AndrewDykstra/Face-Tracking-Camera/opencv/sources/doc/tutorials/imgproc/histograms/back_projection/images/Back_Projection_Theory3.jpg

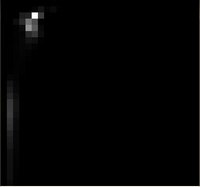
opencv/sources/doc/tutorials/imgproc/histograms/back_projection/images/Back_Projection_Theory3.jpg
