AndrewDykstra/Face-Tracking-Camera/opencv/sources/doc/tutorials/imgproc/histograms/back_projection/images/Back_Projection_Theory4.jpg

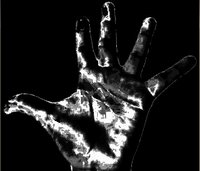
opencv/sources/doc/tutorials/imgproc/histograms/back_projection/images/Back_Projection_Theory4.jpg
