AndrewDykstra/Face-Tracking-Camera/opencv/sources/doc/tutorials/imgproc/histograms/histogram_calculation/images/Histogram_Calculation_Theory_Hist1.jpg

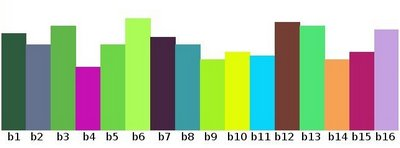
opencv/sources/doc/tutorials/imgproc/histograms/histogram_calculation/images/Histogram_Calculation_Theory_Hist1.jpg
