AndrewDykstra/Face-Tracking-Camera/opencv/sources/doc/tutorials/imgproc/histograms/histogram_equalization/images/Histogram_Equalization_Theory_1.jpg

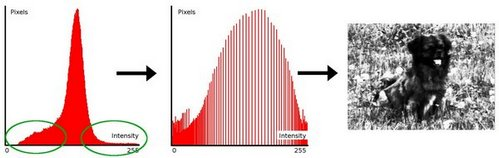
opencv/sources/doc/tutorials/imgproc/histograms/histogram_equalization/images/Histogram_Equalization_Theory_1.jpg
