AndrewDykstra/Face-Tracking-Camera/opencv/sources/doc/tutorials/imgproc/histograms/template_matching/images/Template_Matching_Template_Theory_Summary.jpg

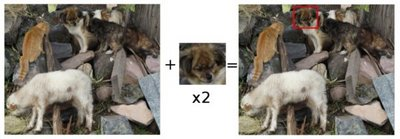
opencv/sources/doc/tutorials/imgproc/histograms/template_matching/images/Template_Matching_Template_Theory_Summary.jpg
