AndrewDykstra/Face-Tracking-Camera/3D Model Parts and Assembly/ArduinoUno/blm21.SLDPRT

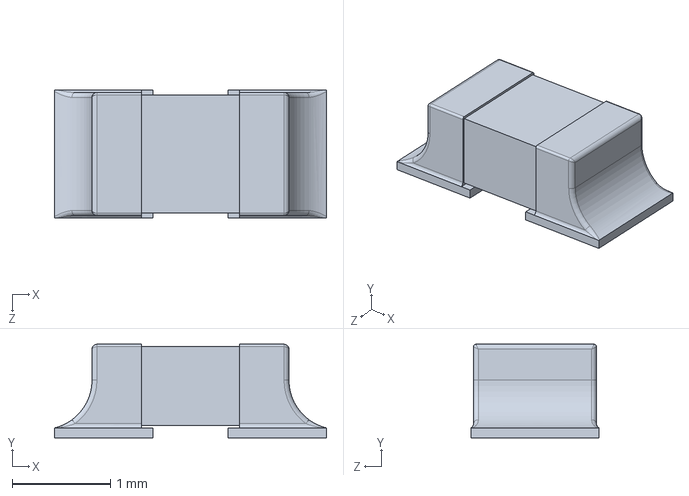
[picture p27: CAD file, 2022-12-01]
3D Model Parts and Assembly/ArduinoUno/blm21.SLDPRT
2.76 x 0.95 x 1.30 mm
