AndrewDykstra/Face-Tracking-Camera/3D Model Parts and Assembly/ArduinoUno/atmega16u2.SLDPRT

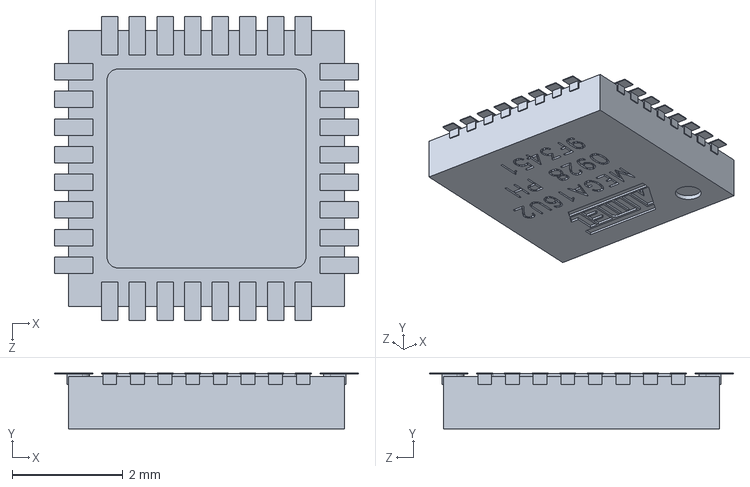
[picture p28: CAD file, 2022-12-01]
3D Model Parts and Assembly/ArduinoUno/atmega16u2.SLDPRT
5.50 x 1.01 x 5.50 mm
