AndrewDykstra/Face-Tracking-Camera/3D Model Parts and Assembly/ArduinoUno/6 PORT HEADER.SLDPRT

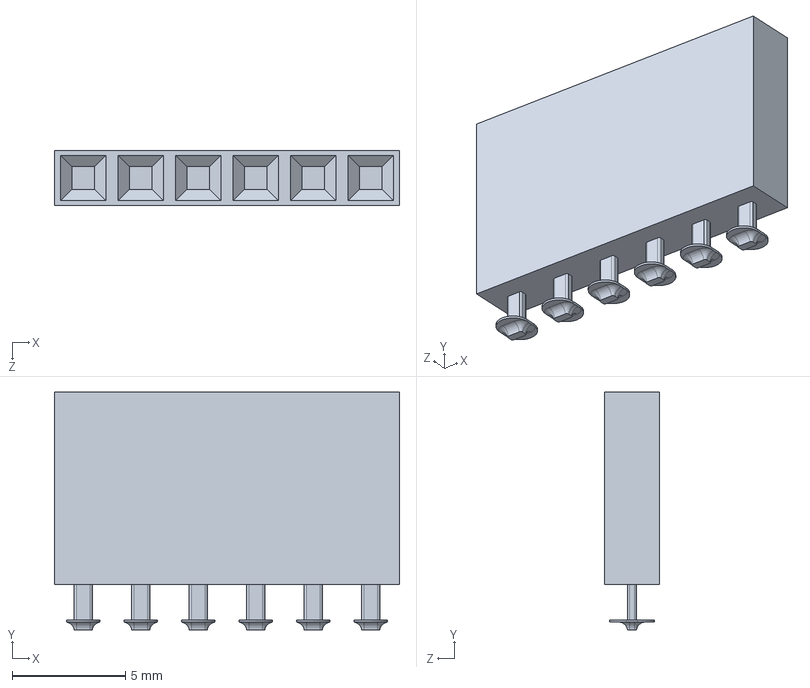
[picture p29: CAD file, 2022-12-01]
3D Model Parts and Assembly/ArduinoUno/6 PORT HEADER.SLDPRT
15.2 x 10.5 x 2.41 mm
