AndrewDykstra/Face-Tracking-Camera/3D Model Parts and Assembly/Logitech_C920.SLDPRT

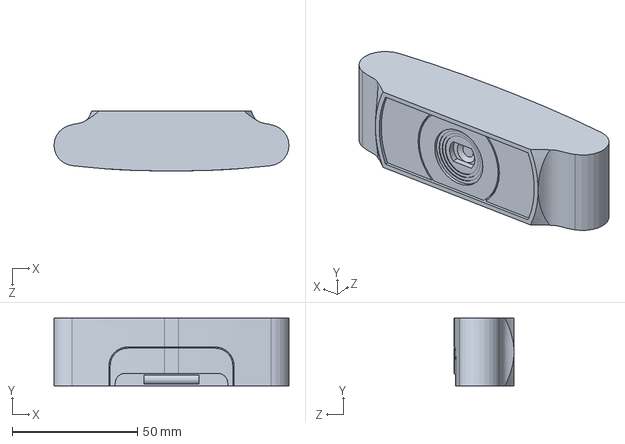
[picture p30: CAD file, 2022-12-01]
3D Model Parts and Assembly/Logitech_C920.SLDPRT
94.0 x 27.0 x 24.0 mm
