AndrewDykstra/Face-Tracking-Camera/3D Model Parts and Assembly/ArduinoUno/603 cap on pad.SLDPRT

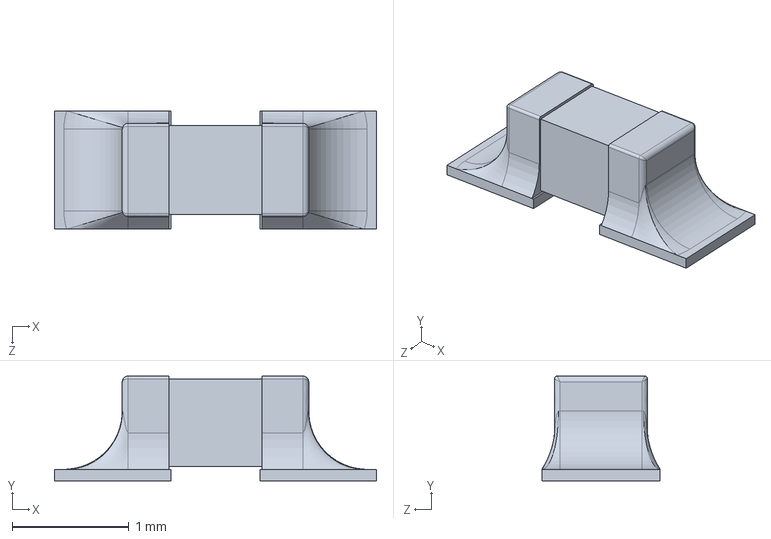
[picture p31: CAD file, 2022-12-01]
3D Model Parts and Assembly/ArduinoUno/603 cap on pad.SLDPRT
2.76 x 0.9 x 1.02 mm
