AndrewDykstra/Face-Tracking-Camera/3D Model Parts and Assembly/pantilt.STEP

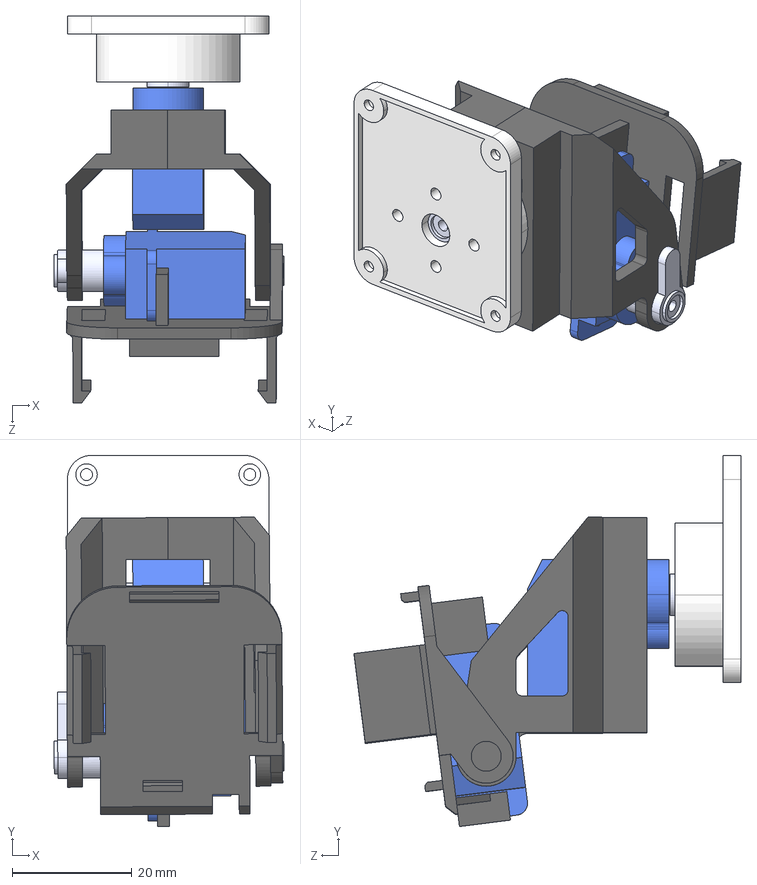
[picture p32: CAD file, 2022-12-01]
3D Model Parts and Assembly/pantilt.STEP
38.4 x 62.1 x 64.7 mm
pantilt_1_Domyslna
servo_emax_9g_horn_Domyslna
servo_emax_9g_main_body_Domyslna x 2
pantilt_2_left_Domyslna
pantilt_2_right_Domyslna
servo_emax_9g_horn_2_Domyslna
pantilt_3_Domyslna
