AndrewDykstra/Face-Tracking-Camera/3D Model Parts and Assembly/ArduinoUno/cd1206 diode.SLDPRT

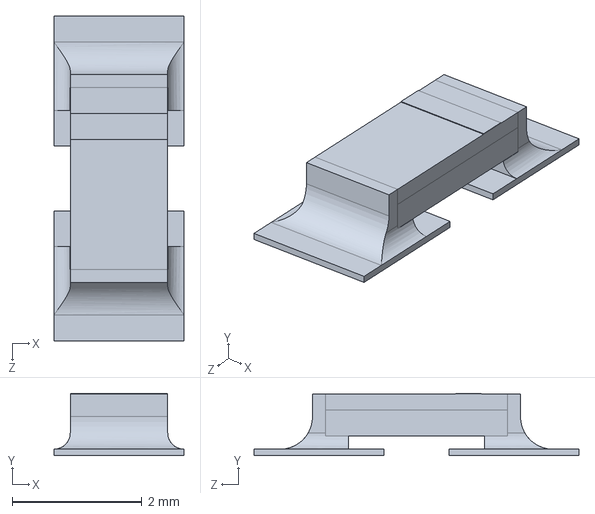
[picture p33: CAD file, 2022-12-01]
3D Model Parts and Assembly/ArduinoUno/cd1206 diode.SLDPRT
2.00 x 0.96 x 5.00 mm
