AndrewDykstra/Face-Tracking-Camera/3D Model Parts and Assembly/IphoneBox.SLDPRT

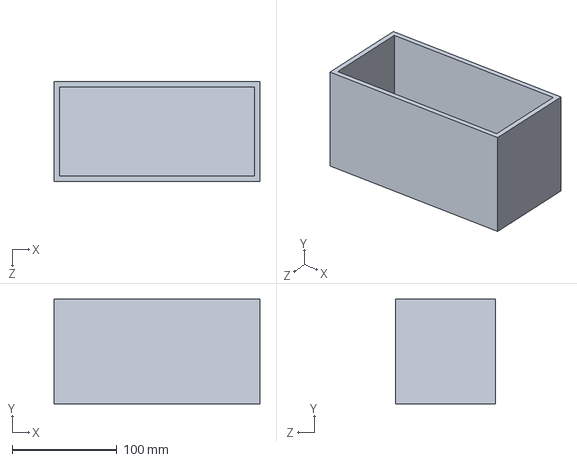
[picture p34: CAD file, 2022-12-01]
3D Model Parts and Assembly/IphoneBox.SLDPRT
196.9 x 100.3 x 95.2 mm
