AndrewDykstra/Face-Tracking-Camera/3D Model Parts and Assembly/ArduinoUno/16mhz crystal - measured.SLDPRT

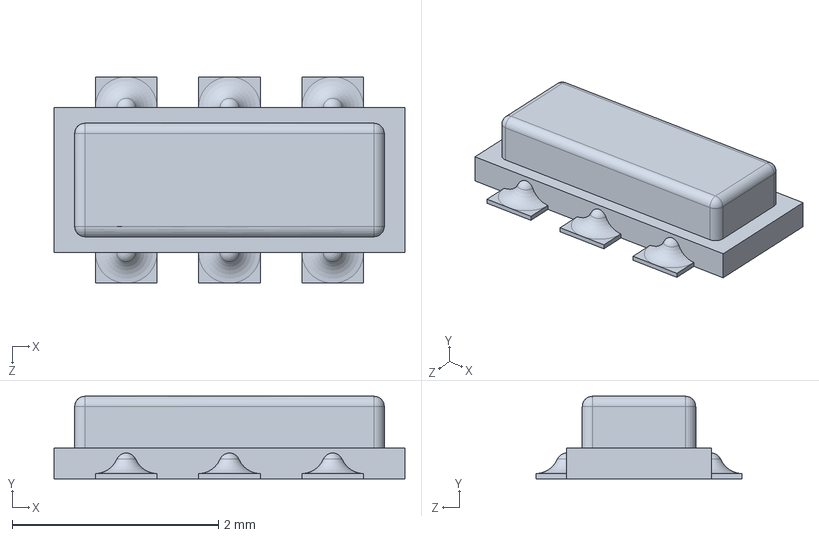
[picture p35: CAD file, 2022-12-01]
3D Model Parts and Assembly/ArduinoUno/16mhz crystal - measured.SLDPRT
3.40 x 0.8 x 2.00 mm
