AndrewDykstra/Face-Tracking-Camera/3D Model Parts and Assembly/pantilt_1.SLDPRT

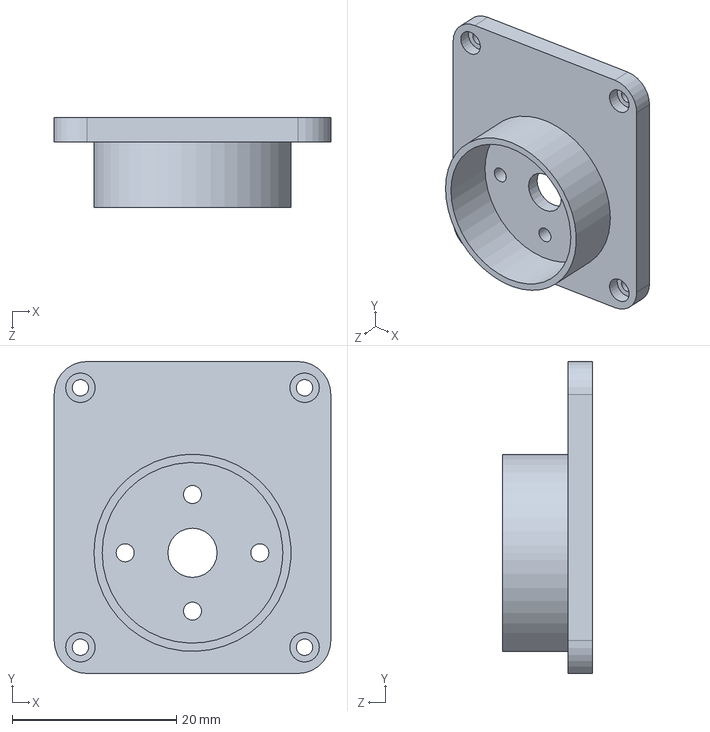
[picture p36: CAD file, 2022-12-01]
3D Model Parts and Assembly/pantilt_1.SLDPRT
33.7 x 38.0 x 11.0 mm
