AndrewDykstra/Face-Tracking-Camera/3D Model Parts and Assembly/ArduinoUno/PADS001.SLDPRT

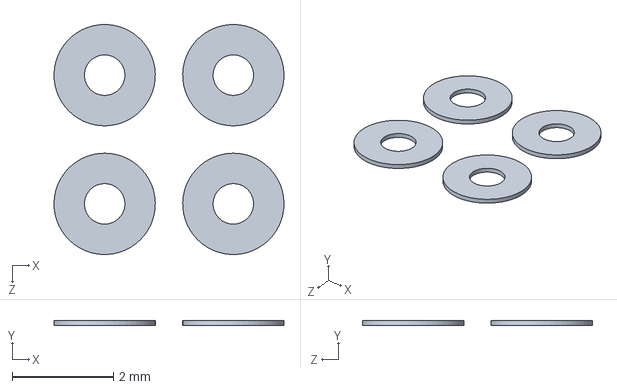
[picture p37: CAD file, 2022-12-01]
3D Model Parts and Assembly/ArduinoUno/PADS001.SLDPRT
4.54 x 0.1 x 4.54 mm
