AndrewDykstra/Face-Tracking-Camera/3D Model Parts and Assembly/pantilt_3.SLDPRT

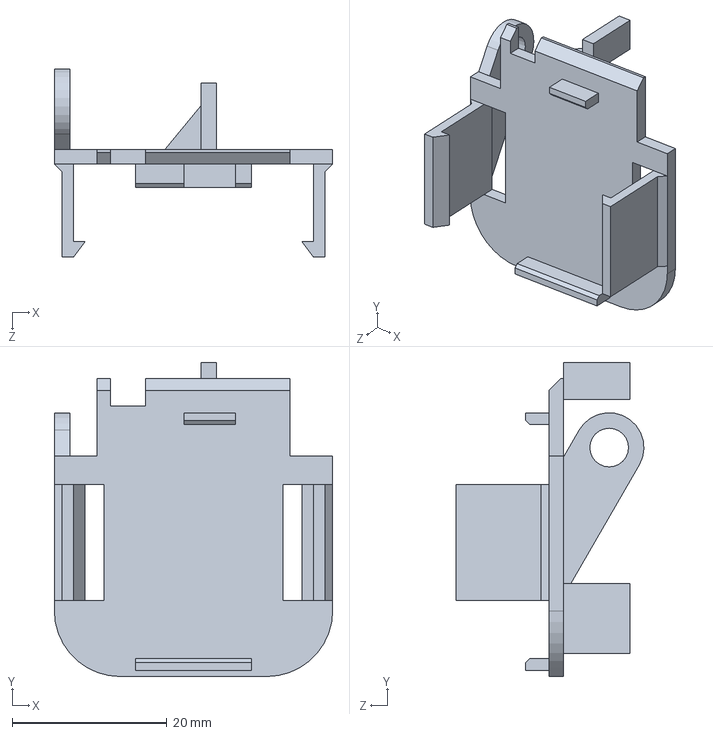
[picture p38: CAD file, 2022-12-01]
3D Model Parts and Assembly/pantilt_3.SLDPRT
36.0 x 40.6 x 24.3 mm
