AndrewDykstra/Face-Tracking-Camera/3D Model Parts and Assembly/pantilt_2_left.SLDPRT

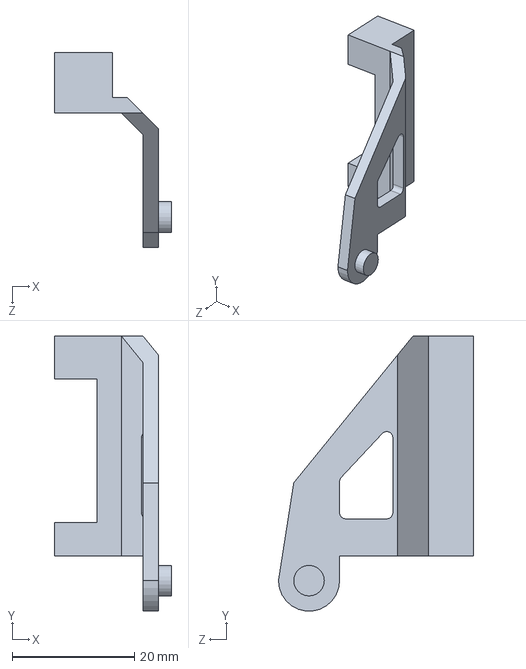
[picture p39: CAD file, 2022-12-01]
3D Model Parts and Assembly/pantilt_2_left.SLDPRT
19.2 x 45.0 x 31.9 mm
