AndrewDykstra/Face-Tracking-Camera/3D Model Parts and Assembly/ArduinoUno/led.SLDPRT

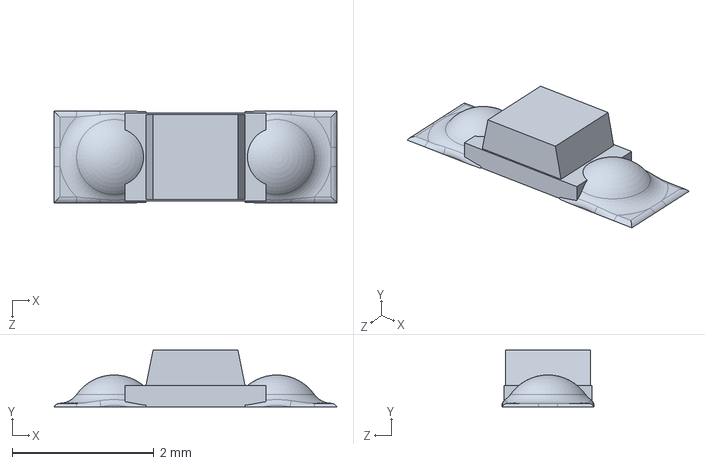
[picture p40: CAD file, 2022-12-01]
3D Model Parts and Assembly/ArduinoUno/led.SLDPRT
4.00 x 0.8 x 1.30 mm
