AndrewDykstra/Face-Tracking-Camera/3D Model Parts and Assembly/Logitech_C920Glass.SLDPRT

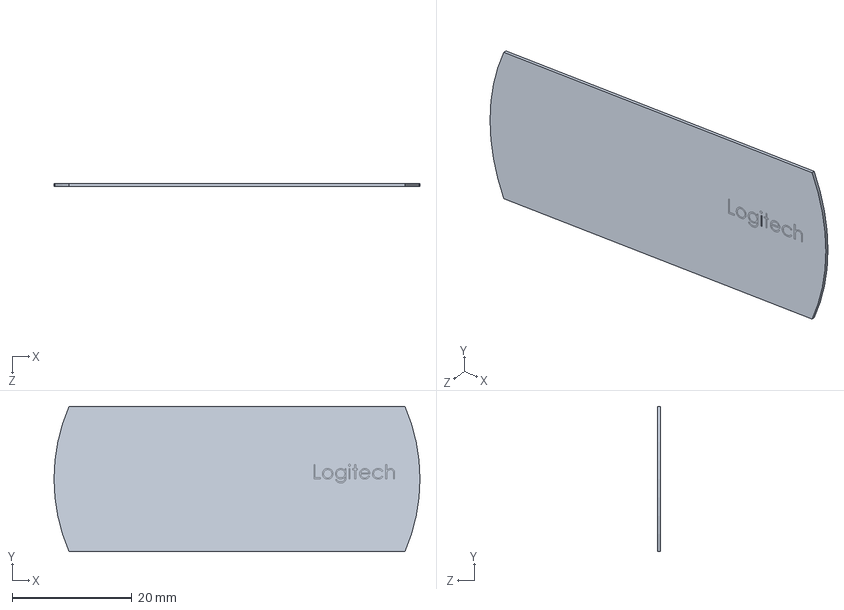
[picture p41: CAD file, 2022-12-01]
3D Model Parts and Assembly/Logitech_C920Glass.SLDPRT
61.0 x 24.2 x 0.51 mm
