AndrewDykstra/Face-Tracking-Camera/3D Model Parts and Assembly/ArduinoUno/10 PORT HEADER.SLDPRT

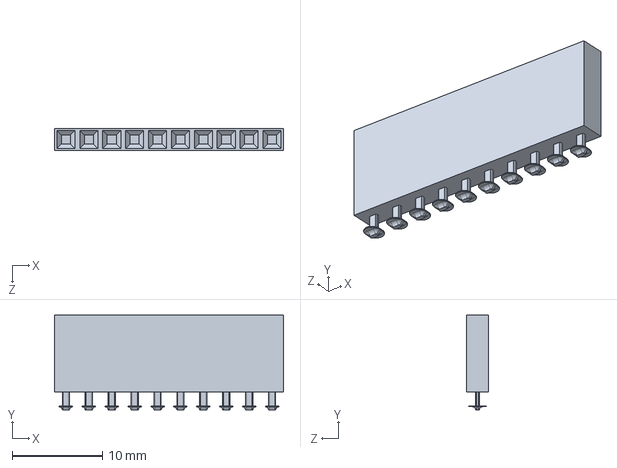
[picture p42: CAD file, 2022-12-01]
3D Model Parts and Assembly/ArduinoUno/10 PORT HEADER.SLDPRT
25.4 x 10.5 x 2.41 mm
