AndrewDykstra/Face-Tracking-Camera/3D Model Parts and Assembly/servo_emax_9g_horn_2.SLDPRT

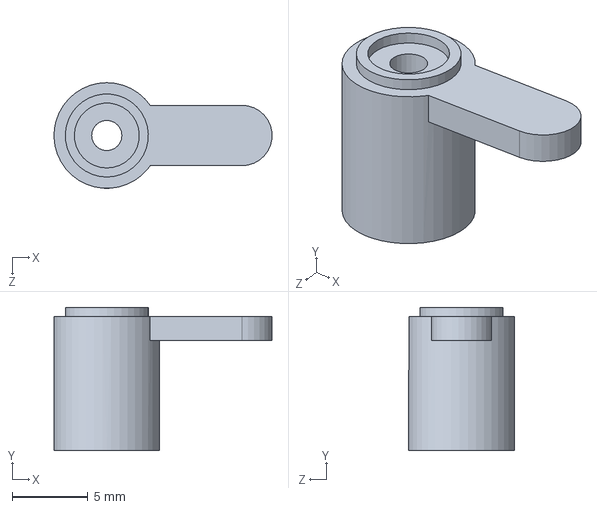
[picture p43: CAD file, 2022-12-01]
3D Model Parts and Assembly/servo_emax_9g_horn_2.SLDPRT
14.4 x 9.50 x 7.00 mm
