AndrewDykstra/Face-Tracking-Camera/3D Model Parts and Assembly/ArduinoUno/crystal.sldprt

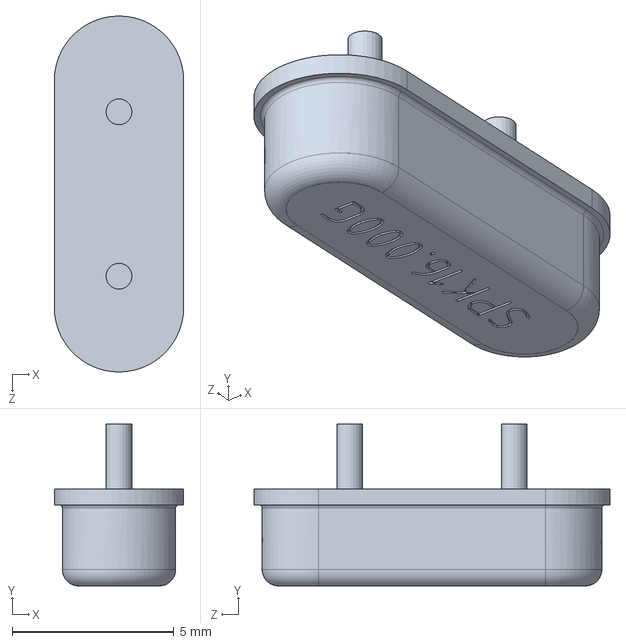
[picture p44: CAD file, 2022-12-01]
3D Model Parts and Assembly/ArduinoUno/crystal.sldprt
4.00 x 5.00 x 11.0 mm
