AndrewDykstra/Face-Tracking-Camera/3D Model Parts and Assembly/servo_emax_9g_horn.SLDPRT

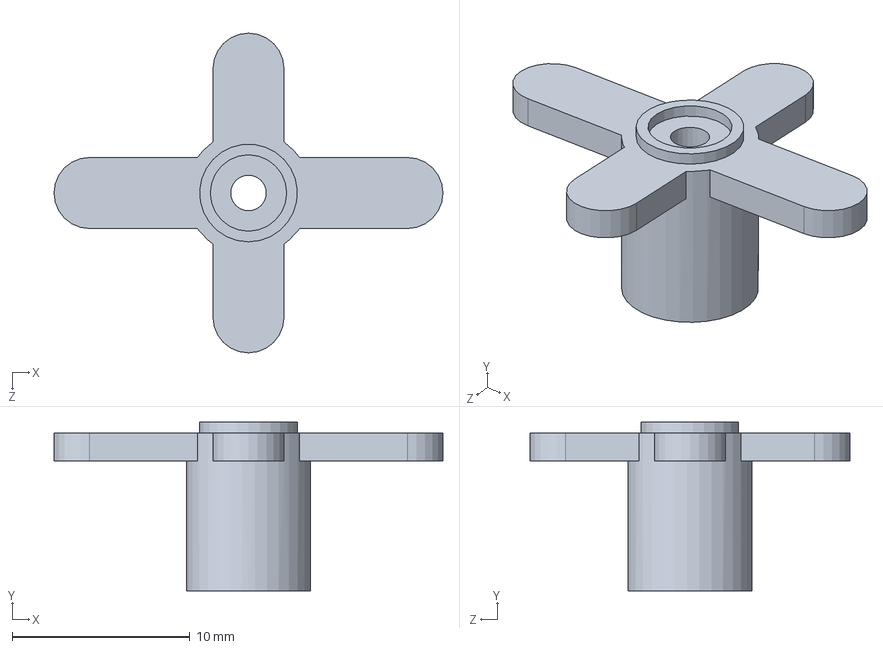
[picture p45: CAD file, 2022-12-01]
3D Model Parts and Assembly/servo_emax_9g_horn.SLDPRT
21.9 x 9.50 x 18.0 mm
