AndrewDykstra/Face-Tracking-Camera/3D Model Parts and Assembly/ArduinoUno/dip socket pin.SLDPRT

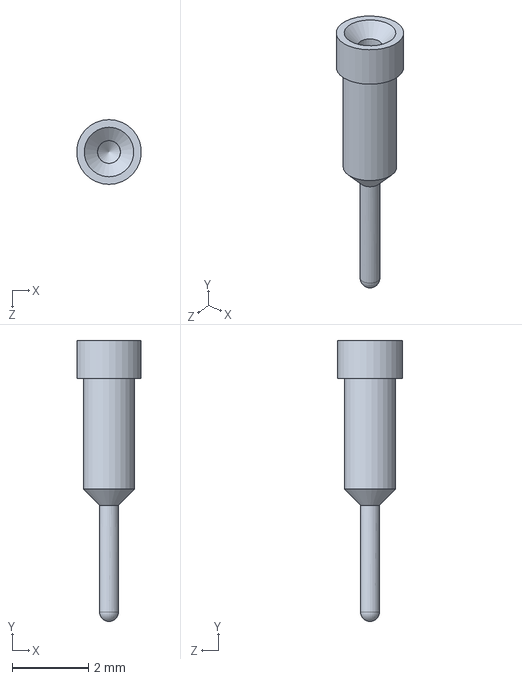
[picture p46: CAD file, 2022-12-01]
3D Model Parts and Assembly/ArduinoUno/dip socket pin.SLDPRT
1.69 x 7.37 x 1.70 mm
