AndrewDykstra/Face-Tracking-Camera/3D Model Parts and Assembly/matrix.SLDPRT

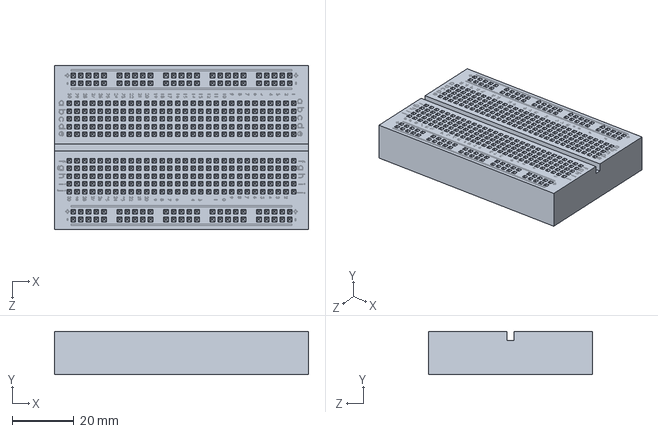
[picture p47: CAD file, 2022-12-01]
3D Model Parts and Assembly/matrix.SLDPRT
82.0 x 14.0 x 53.0 mm
