AndrewDykstra/Face-Tracking-Camera/3D Model Parts and Assembly/ArduinoUno/103 RESISTOR PACK.SLDPRT

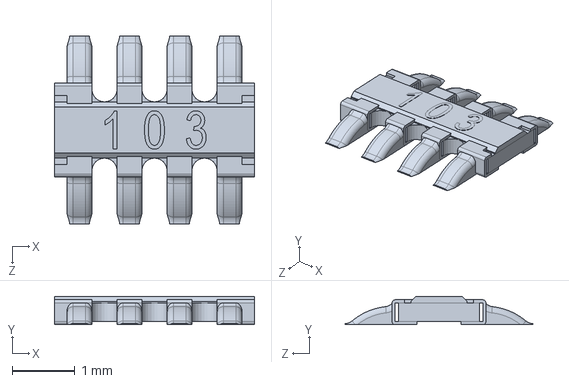
[picture p48: CAD file, 2022-12-01]
3D Model Parts and Assembly/ArduinoUno/103 RESISTOR PACK.SLDPRT
3.20 x 0.455 x 3.00 mm
