AndrewDykstra/Face-Tracking-Camera/3D Model Parts and Assembly/ArduinoUno/RESET CORE.SLDPRT

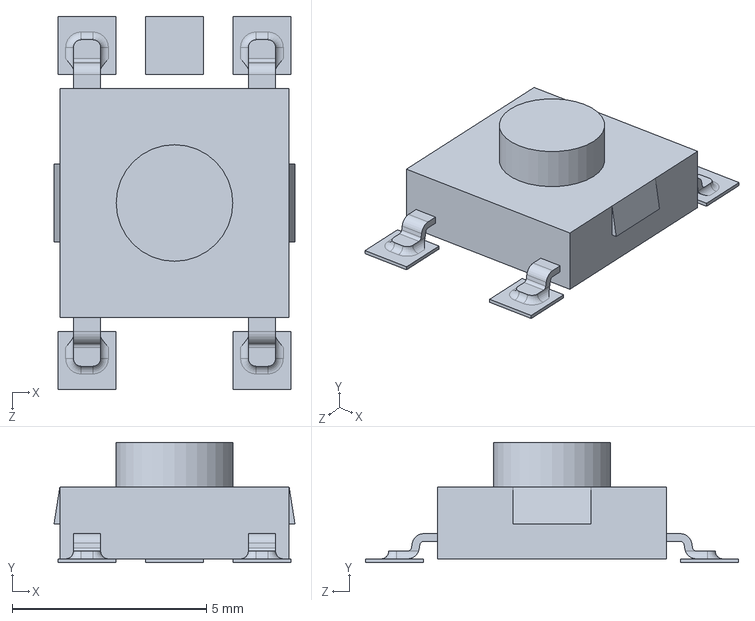
[picture p49: CAD file, 2022-12-01]
3D Model Parts and Assembly/ArduinoUno/RESET CORE.SLDPRT
6.20 x 3.10 x 9.60 mm
