AndrewDykstra/Face-Tracking-Camera/3D Model Parts and Assembly/ArduinoUno/usb top contact.SLDPRT

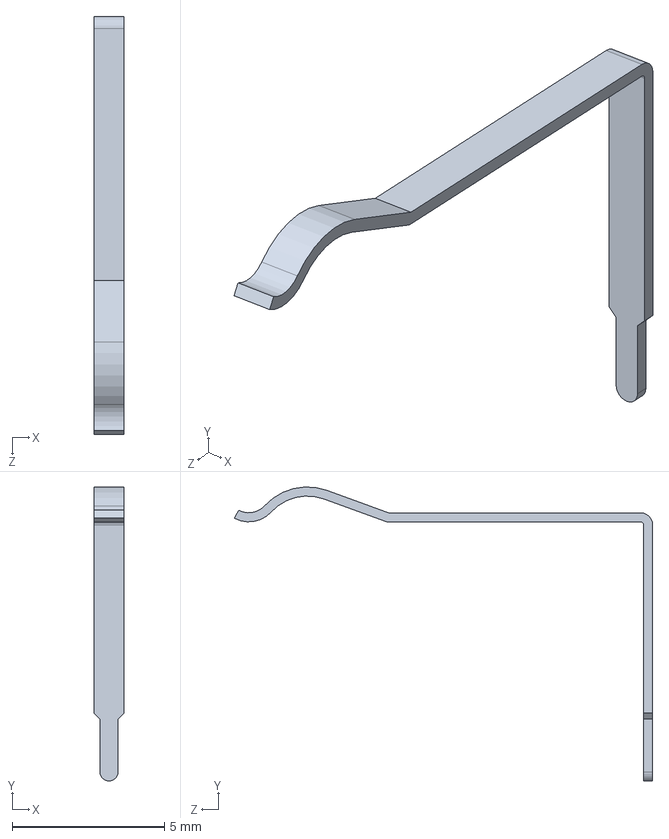
[picture p50: CAD file, 2022-12-01]
3D Model Parts and Assembly/ArduinoUno/usb top contact.SLDPRT
1.00 x 9.67 x 13.8 mm
