AndrewDykstra/Face-Tracking-Camera/3D Model Parts and Assembly/ArduinoUno/usb btm contact.SLDPRT

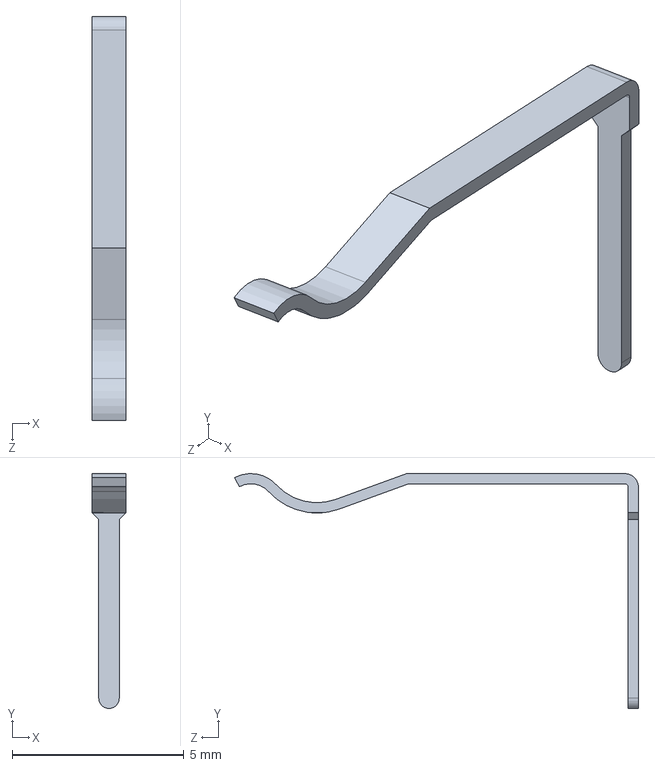
[picture p51: CAD file, 2022-12-01]
3D Model Parts and Assembly/ArduinoUno/usb btm contact.SLDPRT
1.00 x 6.84 x 11.8 mm
