AndrewDykstra/Face-Tracking-Camera/3D Model Parts and Assembly/ArduinoUno/lp2985dgkr.SLDPRT

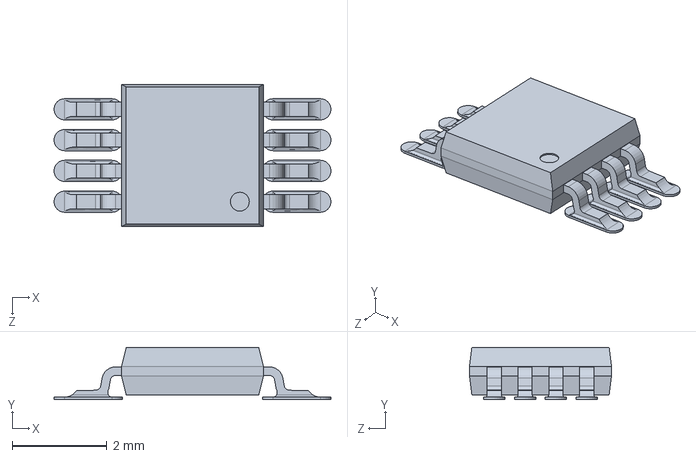
[picture p52: CAD file, 2022-12-01]
3D Model Parts and Assembly/ArduinoUno/lp2985dgkr.SLDPRT
5.85 x 1.10 x 3.00 mm
