AndrewDykstra/Face-Tracking-Camera/3D Model Parts and Assembly/ArduinoUno/mf-msmf050-2.SLDPRT

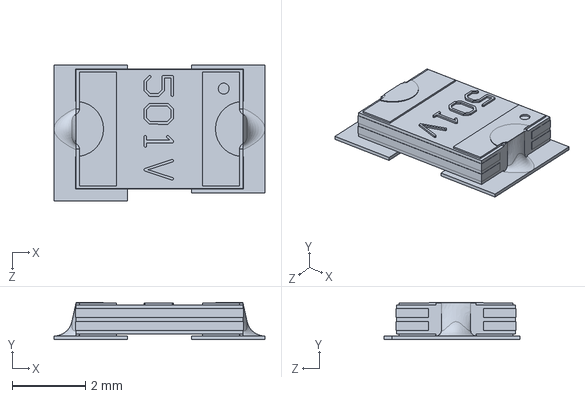
[picture p53: CAD file, 2022-12-01]
3D Model Parts and Assembly/ArduinoUno/mf-msmf050-2.SLDPRT
5.75 x 1.02 x 3.72 mm
