AndrewDykstra/Face-Tracking-Camera/3D Model Parts and Assembly/ArduinoUno/nano - reg.SLDPRT

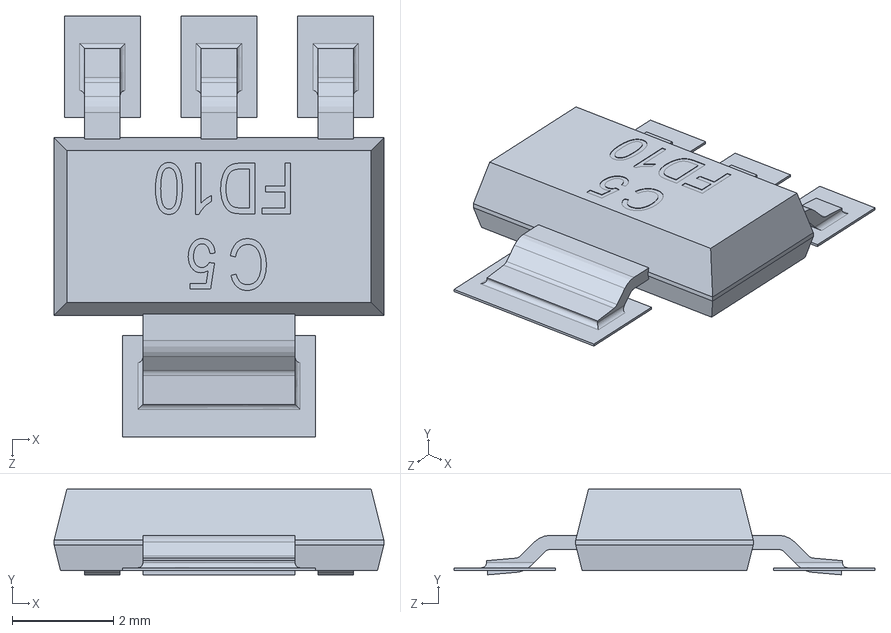
[picture p54: CAD file, 2022-12-01]
3D Model Parts and Assembly/ArduinoUno/nano - reg.SLDPRT
6.50 x 1.69 x 8.30 mm
