AndrewDykstra/Face-Tracking-Camera/3D Model Parts and Assembly/ArduinoUno/ATMEL328P.SLDPRT

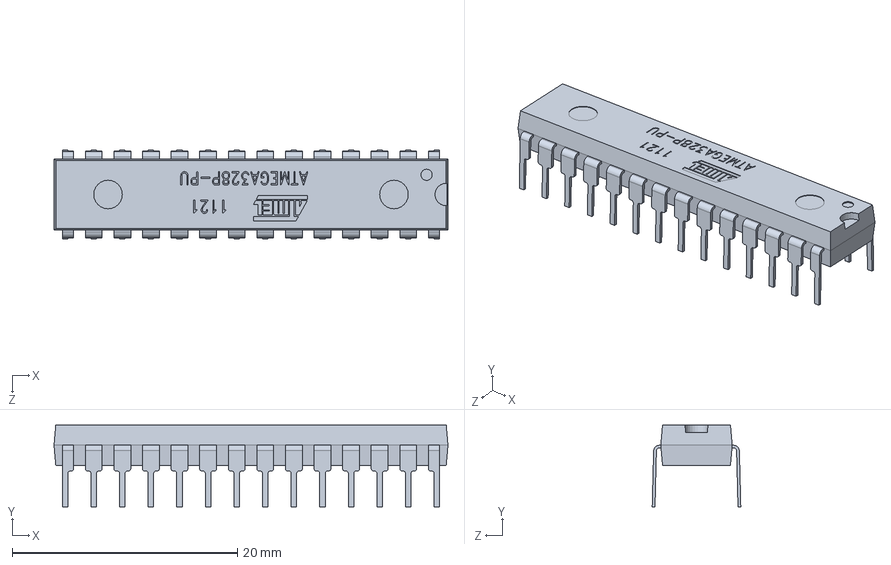
[picture p55: CAD file, 2022-12-01]
3D Model Parts and Assembly/ArduinoUno/ATMEL328P.SLDPRT
35.0 x 7.27 x 7.87 mm
