AndrewDykstra/Face-Tracking-Camera/3D Model Parts and Assembly/ArduinoUno/47uf CAP Dcase.SLDPRT

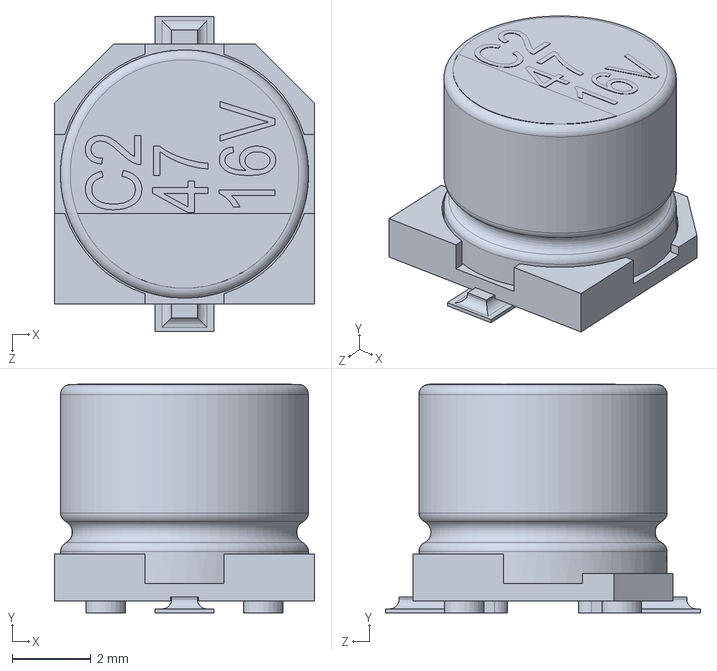
[picture p56: CAD file, 2022-12-01]
3D Model Parts and Assembly/ArduinoUno/47uf CAP Dcase.SLDPRT
6.60 x 5.81 x 8.00 mm
