AndrewDykstra/Face-Tracking-Camera/3D Model Parts and Assembly/ArduinoUno/m7 diode.SLDPRT

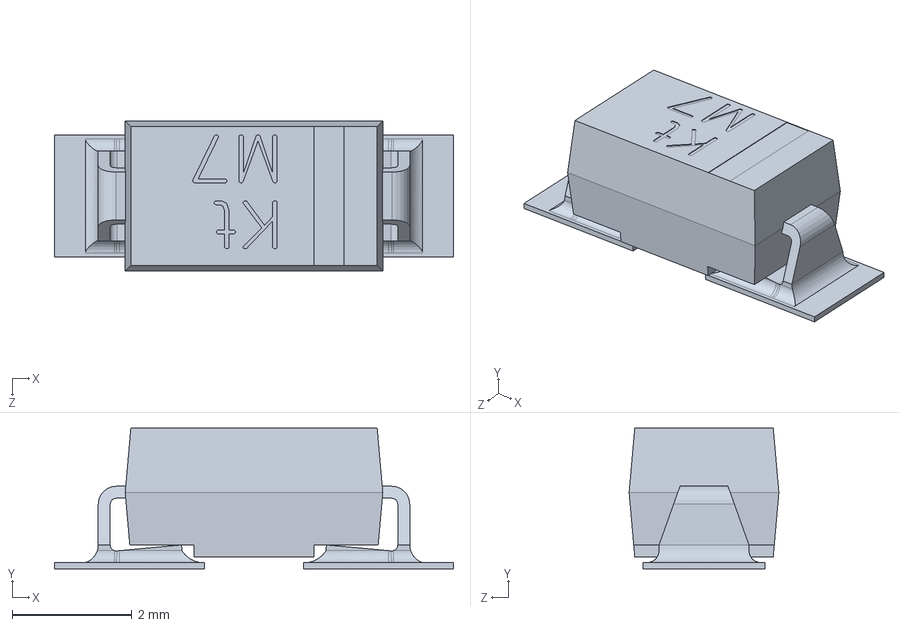
[picture p57: CAD file, 2022-12-01]
3D Model Parts and Assembly/ArduinoUno/m7 diode.SLDPRT
6.66 x 2.35 x 2.50 mm
