AndrewDykstra/Face-Tracking-Camera/3D Model Parts and Assembly/ArduinoUno/USB core.SLDPRT

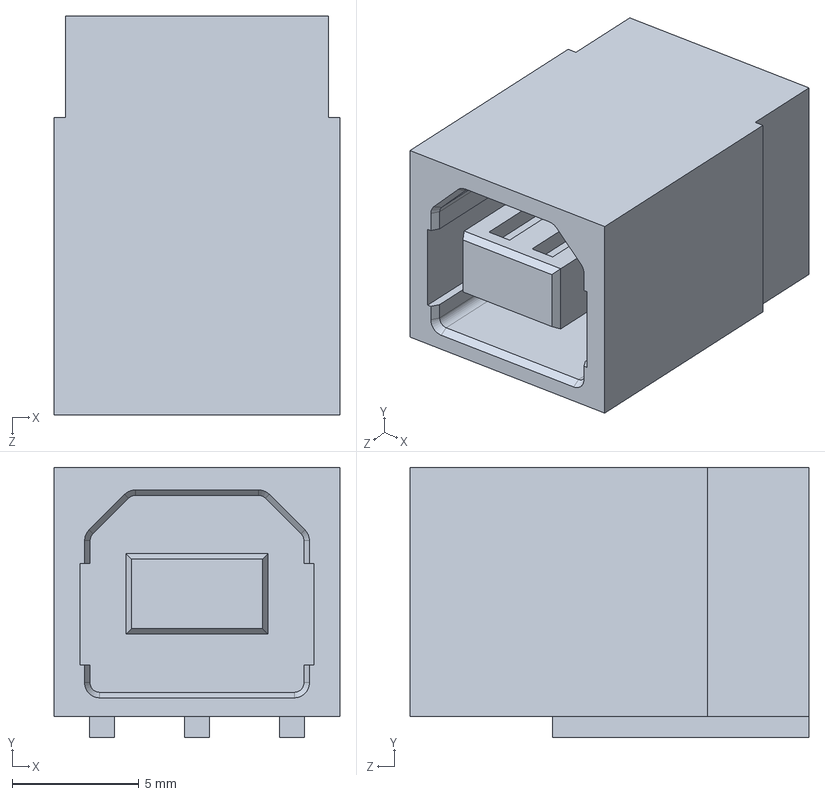
[picture p58: CAD file, 2022-12-01]
3D Model Parts and Assembly/ArduinoUno/USB core.SLDPRT
11.3 x 10.7 x 15.8 mm
