AndrewDykstra/Face-Tracking-Camera/3D Model Parts and Assembly/ArduinoUno/MLC0603.SLDPRT

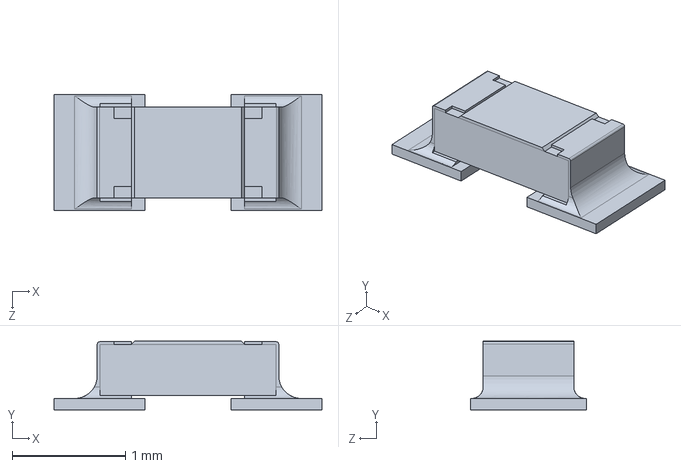
[picture p59: CAD file, 2022-12-01]
3D Model Parts and Assembly/ArduinoUno/MLC0603.SLDPRT
2.36 x 0.605 x 1.02 mm
