AndrewDykstra/Face-Tracking-Camera/3D Model Parts and Assembly/ArduinoUno/lmv358.SLDPRT

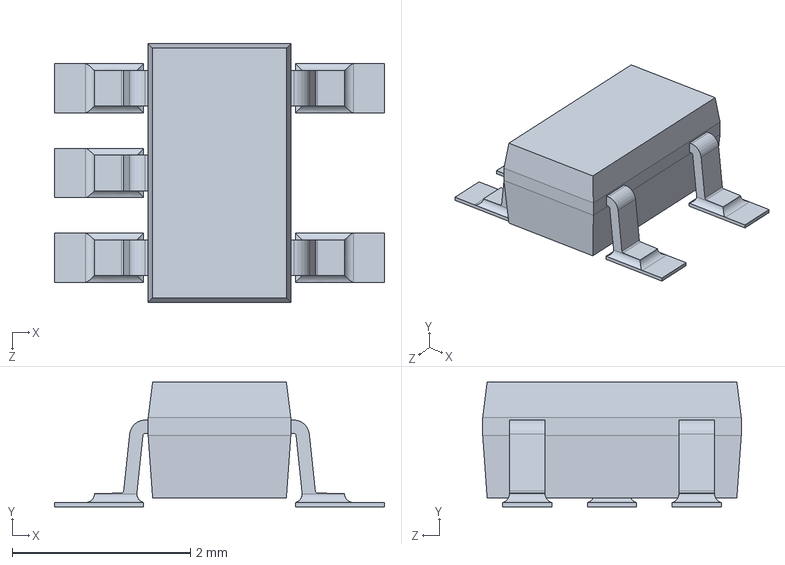
[picture p60: CAD file, 2022-12-01]
3D Model Parts and Assembly/ArduinoUno/lmv358.SLDPRT
3.70 x 1.40 x 2.90 mm
