AndrewDykstra/Face-Tracking-Camera/3D Model Parts and Assembly/ArduinoUno/ssot3.SLDPRT

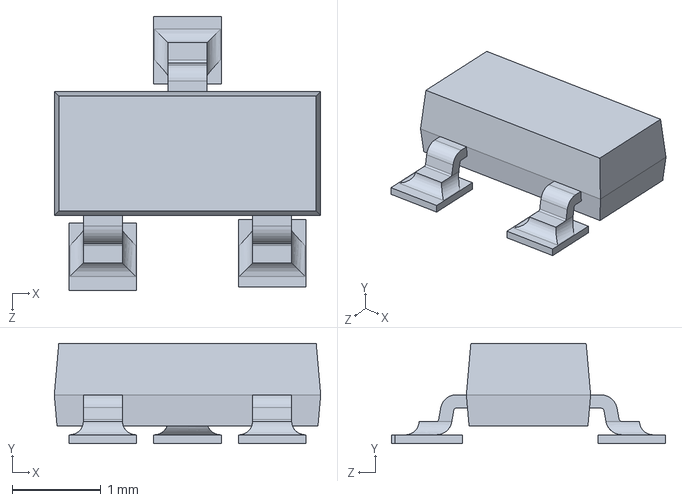
[picture p61: CAD file, 2022-12-01]
3D Model Parts and Assembly/ArduinoUno/ssot3.SLDPRT
3.00 x 1.13 x 3.09 mm
