AndrewDykstra/Face-Tracking-Camera/3D Model Parts and Assembly/ArduinoUno/8 PORT HEADER.SLDPRT

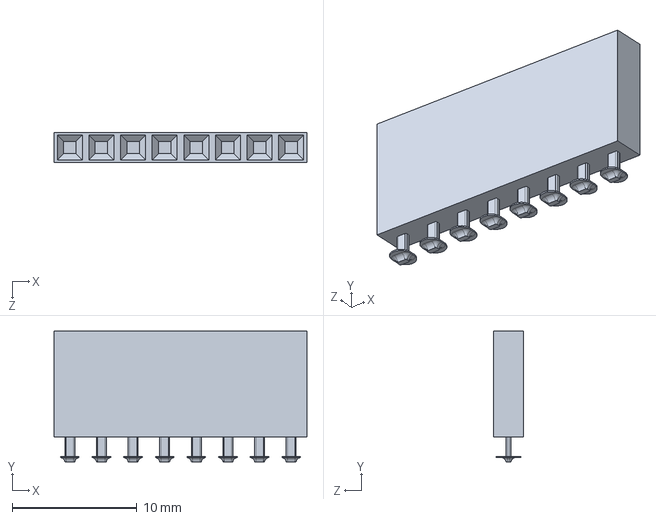
[picture p62: CAD file, 2022-12-01]
3D Model Parts and Assembly/ArduinoUno/8 PORT HEADER.SLDPRT
20.3 x 10.5 x 2.41 mm
