AndrewDykstra/Face-Tracking-Camera/3D Model Parts and Assembly/ArduinoUno/RESET.SLDPRT

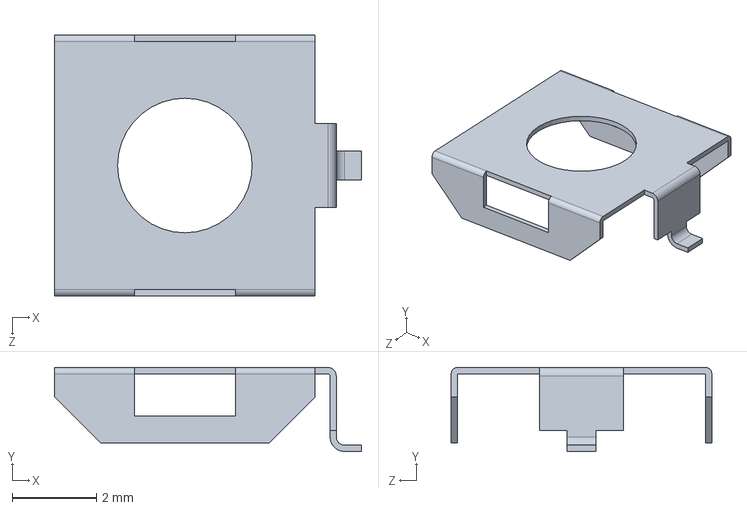
[picture p63: CAD file, 2022-12-01]
3D Model Parts and Assembly/ArduinoUno/RESET.SLDPRT
7.30 x 2.00 x 6.20 mm
