AndrewDykstra/Face-Tracking-Camera/3D Model Parts and Assembly/ArduinoUno/USB SHELL.SLDPRT

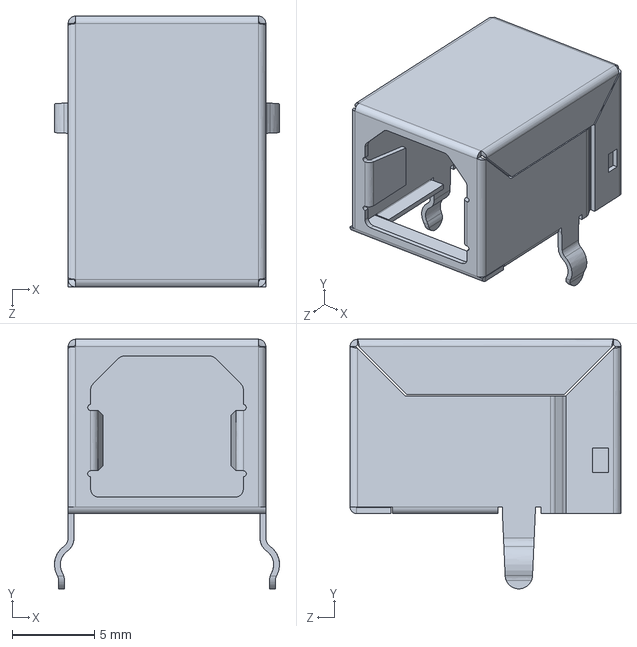
[picture p64: CAD file, 2022-12-01]
3D Model Parts and Assembly/ArduinoUno/USB SHELL.SLDPRT
13.7 x 15.2 x 16.5 mm
