AndrewDykstra/Face-Tracking-Camera/3D Model Parts and Assembly/ArduinoUno/603 resistor.SLDPRT

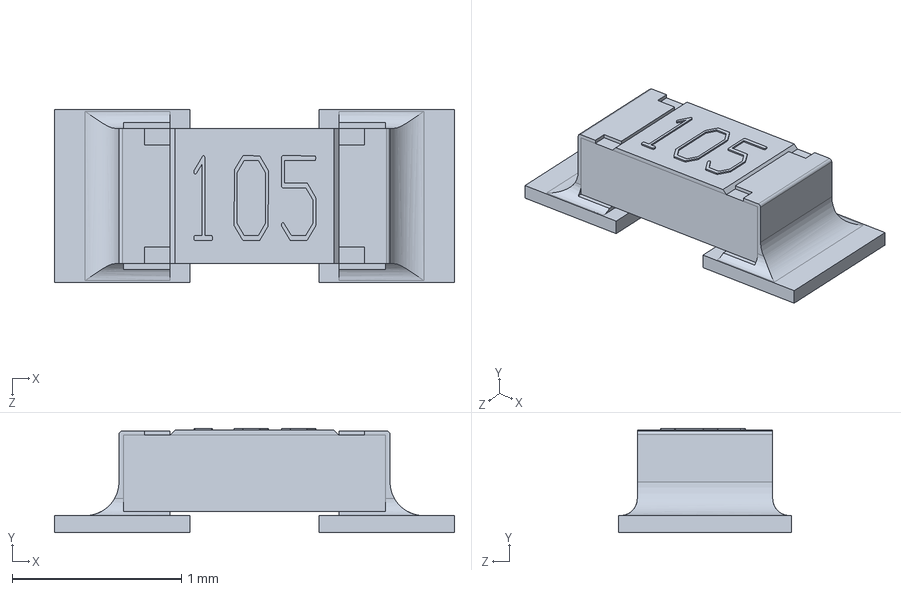
[picture p65: CAD file, 2022-12-01]
3D Model Parts and Assembly/ArduinoUno/603 resistor.SLDPRT
2.36 x 0.615 x 1.02 mm
