AndrewDykstra/Face-Tracking-Camera/opencv/sources/doc/tutorials/contrib/retina_model/images/studentsSample_input.jpg

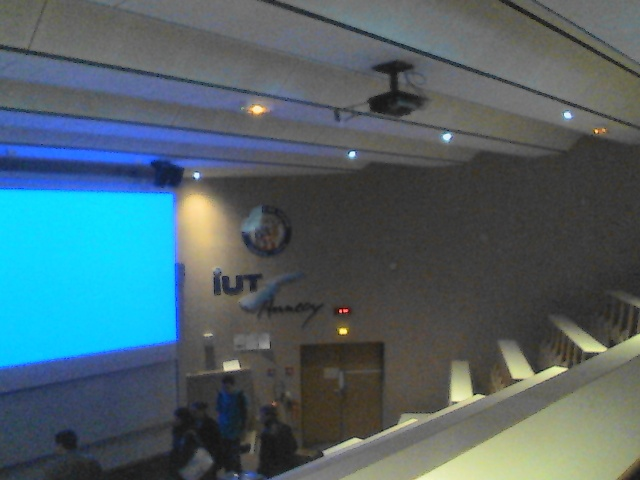
opencv/sources/doc/tutorials/contrib/retina_model/images/studentsSample_input.jpg
