AndrewDykstra/Face-Tracking-Camera/opencv/sources/doc/tutorials/core/adding_images/images/Adding_Images_Tutorial_Result_0.jpg

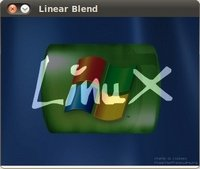
opencv/sources/doc/tutorials/core/adding_images/images/Adding_Images_Tutorial_Result_0.jpg
