AndrewDykstra/Face-Tracking-Camera/opencv/sources/doc/tutorials/core/basic_geometric_drawing/images/Drawing_1_Tutorial_Result_0.png

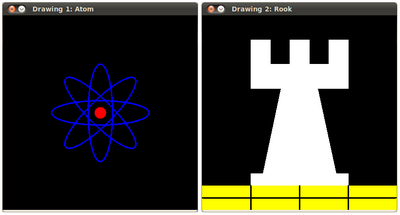
opencv/sources/doc/tutorials/core/basic_geometric_drawing/images/Drawing_1_Tutorial_Result_0.png
