AndrewDykstra/Face-Tracking-Camera/opencv/sources/doc/tutorials/core/interoperability_with_OpenCV_1/images/outputInteropOpenCV1.jpg

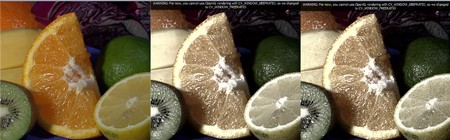
opencv/sources/doc/tutorials/core/interoperability_with_OpenCV_1/images/outputInteropOpenCV1.jpg
