AndrewDykstra/Face-Tracking-Camera/opencv/sources/doc/tutorials/core/random_generator_and_text/images/Drawing_2_Tutorial_Result_2.jpg

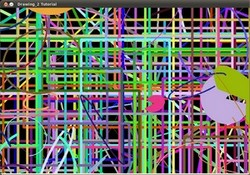
opencv/sources/doc/tutorials/core/random_generator_and_text/images/Drawing_2_Tutorial_Result_2.jpg
