AndrewDykstra/Face-Tracking-Camera/opencv/sources/doc/tutorials/core/table_of_content_core/images/discrete_fourier_transform.png

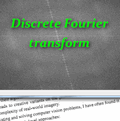
opencv/sources/doc/tutorials/core/table_of_content_core/images/discrete_fourier_transform.png
