AndrewDykstra/Face-Tracking-Camera/opencv/sources/doc/tutorials/core/table_of_content_core/images/file_input_output_with_xml_yml.png

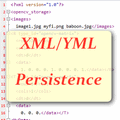
opencv/sources/doc/tutorials/core/table_of_content_core/images/file_input_output_with_xml_yml.png
