AndrewDykstra/Face-Tracking-Camera/opencv/sources/doc/tutorials/core/table_of_content_core/images/matMaskFilter2DOp.png

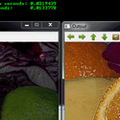
opencv/sources/doc/tutorials/core/table_of_content_core/images/matMaskFilter2DOp.png
