AndrewDykstra/Face-Tracking-Camera/opencv/sources/doc/tutorials/features2d/table_of_content_features2d/images/Feature_Detection_Tutorial_Cover.jpg

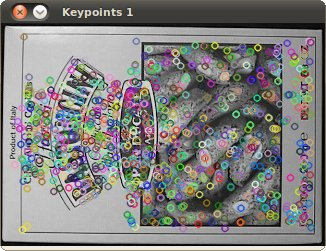
opencv/sources/doc/tutorials/features2d/table_of_content_features2d/images/Feature_Detection_Tutorial_Cover.jpg
