AndrewDykstra/Face-Tracking-Camera/opencv/sources/doc/tutorials/features2d/trackingmotion/corner_subpixeles/images/Corner_Subpixeles_Original_Image.jpg

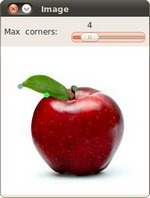
opencv/sources/doc/tutorials/features2d/trackingmotion/corner_subpixeles/images/Corner_Subpixeles_Original_Image.jpg
