AndrewDykstra/Face-Tracking-Camera/opencv/sources/doc/tutorials/features2d/trackingmotion/harris_detector/images/Harris_Detector_Original_Image.jpg

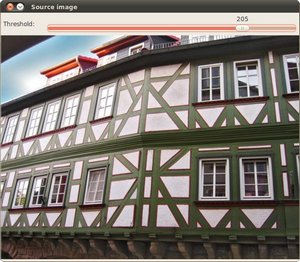
opencv/sources/doc/tutorials/features2d/trackingmotion/harris_detector/images/Harris_Detector_Original_Image.jpg
