AndrewDykstra/Face-Tracking-Camera/opencv/sources/doc/tutorials/highgui/table_of_content_highgui/images/video-write.png

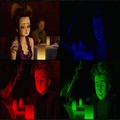
opencv/sources/doc/tutorials/highgui/table_of_content_highgui/images/video-write.png
