AndrewDykstra/Face-Tracking-Camera/opencv/sources/doc/tutorials/highgui/video-input-psnr-ssim/images/outputVideoInput.png

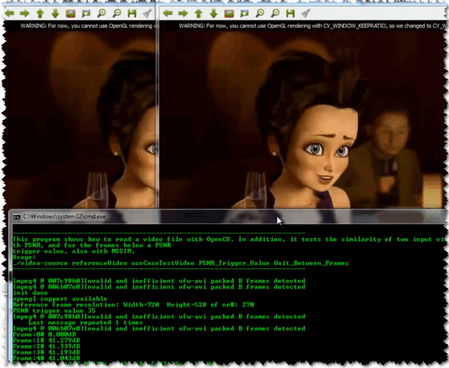
opencv/sources/doc/tutorials/highgui/video-input-psnr-ssim/images/outputVideoInput.png
