AndrewDykstra/Face-Tracking-Camera/opencv/sources/doc/tutorials/highgui/video-write/images/videoCompressSelect.png

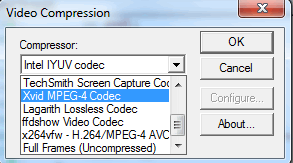
opencv/sources/doc/tutorials/highgui/video-write/images/videoCompressSelect.png
