AndrewDykstra/Face-Tracking-Camera/opencv/sources/doc/tutorials/highgui/video-write/images/videoFileStructure.png

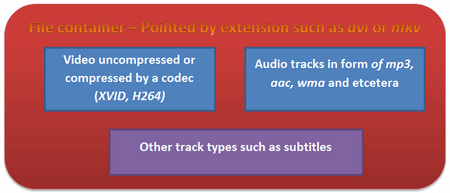
opencv/sources/doc/tutorials/highgui/video-write/images/videoFileStructure.png
