AndrewDykstra/Face-Tracking-Camera/opencv/sources/doc/tutorials/images/core.jpg

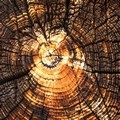
opencv/sources/doc/tutorials/images/core.jpg
