AndrewDykstra/Face-Tracking-Camera/opencv/sources/doc/tutorials/images/general.jpg

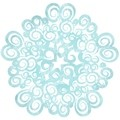
opencv/sources/doc/tutorials/images/general.jpg
