AndrewDykstra/Face-Tracking-Camera/opencv/sources/doc/tutorials/images/highgui.jpg

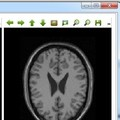
opencv/sources/doc/tutorials/images/highgui.jpg
