AndrewDykstra/Face-Tracking-Camera/opencv/sources/doc/tutorials/images/ml.jpg

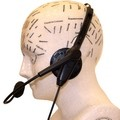
opencv/sources/doc/tutorials/images/ml.jpg
