AndrewDykstra/Face-Tracking-Camera/opencv/sources/doc/tutorials/images/opencv_ios.png

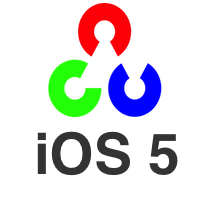
opencv/sources/doc/tutorials/images/opencv_ios.png
