AndrewDykstra/Face-Tracking-Camera/opencv/sources/doc/tutorials/images/retina.jpg

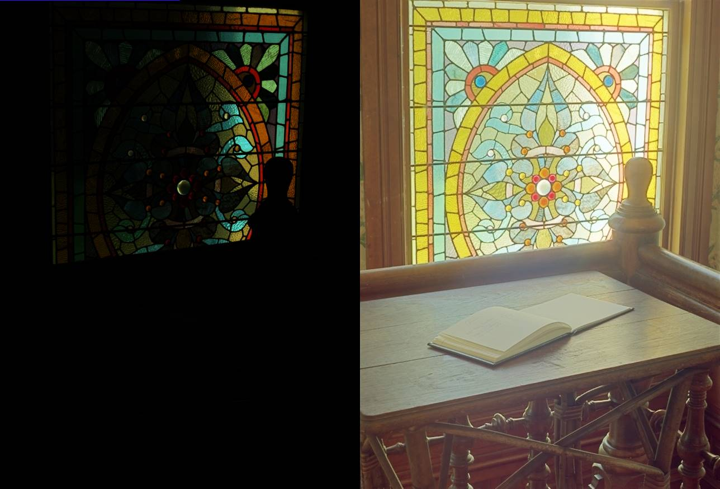
opencv/sources/doc/tutorials/images/retina.jpg
