AndrewDykstra/Face-Tracking-Camera/opencv/sources/doc/tutorials/images/video.jpg

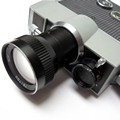
opencv/sources/doc/tutorials/images/video.jpg
