AndrewDykstra/Face-Tracking-Camera/opencv/sources/doc/tutorials/images/viz.jpg

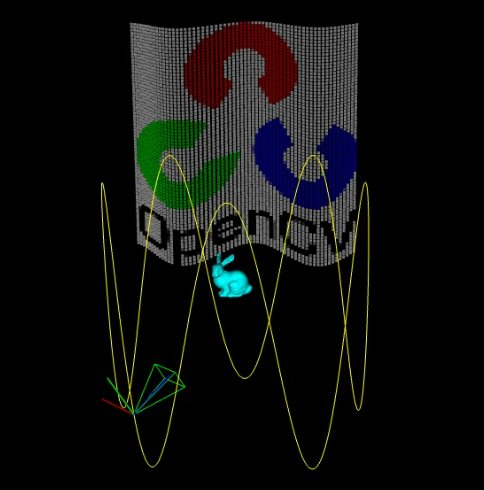
opencv/sources/doc/tutorials/images/viz.jpg
