AndrewDykstra/Face-Tracking-Camera/opencv/sources/doc/tutorials/imgproc/erosion_dilatation/images/Morphology_1_Tutorial_Cover.jpg

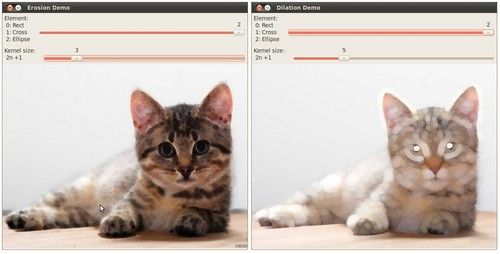
opencv/sources/doc/tutorials/imgproc/erosion_dilatation/images/Morphology_1_Tutorial_Cover.jpg
