AndrewDykstra/Face-Tracking-Camera/opencv/sources/doc/tutorials/imgproc/erosion_dilatation/images/Morphology_1_Tutorial_Original_Image.jpg

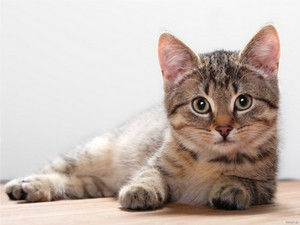
opencv/sources/doc/tutorials/imgproc/erosion_dilatation/images/Morphology_1_Tutorial_Original_Image.jpg
