AndrewDykstra/Face-Tracking-Camera/opencv/sources/doc/tutorials/imgproc/erosion_dilatation/images/Morphology_1_Tutorial_Theory_Dilatation_2.png

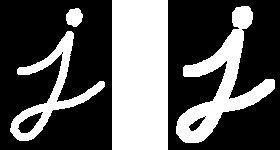
opencv/sources/doc/tutorials/imgproc/erosion_dilatation/images/Morphology_1_Tutorial_Theory_Dilatation_2.png
