AndrewDykstra/Face-Tracking-Camera/opencv/sources/doc/tutorials/imgproc/gausian_median_blur_bilateral_filter/images/Smoothing_Tutorial_theory_gaussian_0.jpg

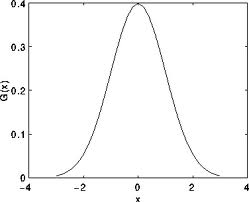
opencv/sources/doc/tutorials/imgproc/gausian_median_blur_bilateral_filter/images/Smoothing_Tutorial_theory_gaussian_0.jpg
