AndrewDykstra/Face-Tracking-Camera/opencv/sources/doc/tutorials/imgproc/histograms/back_projection/images/Back_Projection1_Source_Image.jpg

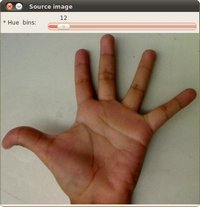
opencv/sources/doc/tutorials/imgproc/histograms/back_projection/images/Back_Projection1_Source_Image.jpg
