AndrewDykstra/Face-Tracking-Camera/opencv/sources/doc/tutorials/imgproc/histograms/back_projection/images/Back_Projection2_Mask.jpg

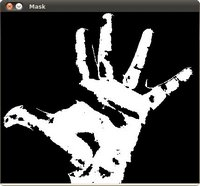
opencv/sources/doc/tutorials/imgproc/histograms/back_projection/images/Back_Projection2_Mask.jpg
