AndrewDykstra/Face-Tracking-Camera/opencv/sources/doc/tutorials/imgproc/histograms/histogram_comparison/images/Histogram_Comparison_Source_0.jpg

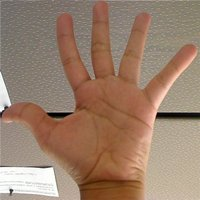
opencv/sources/doc/tutorials/imgproc/histograms/histogram_comparison/images/Histogram_Comparison_Source_0.jpg
