AndrewDykstra/Face-Tracking-Camera/opencv/sources/doc/tutorials/imgproc/histograms/histogram_equalization/images/Histogram_Equalization_Equalized_Histogram.jpg

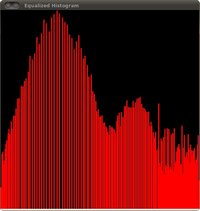
opencv/sources/doc/tutorials/imgproc/histograms/histogram_equalization/images/Histogram_Equalization_Equalized_Histogram.jpg
