AndrewDykstra/Face-Tracking-Camera/opencv/sources/doc/tutorials/imgproc/imgtrans/hough_lines/images/Hough_Lines_Tutorial_Theory_2.jpg

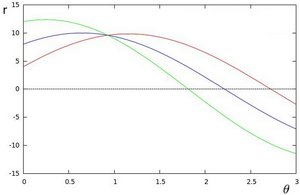
opencv/sources/doc/tutorials/imgproc/imgtrans/hough_lines/images/Hough_Lines_Tutorial_Theory_2.jpg
