AndrewDykstra/Face-Tracking-Camera/opencv/sources/doc/tutorials/imgproc/imgtrans/remap/images/Remap_Tutorial_Original_Image.jpg

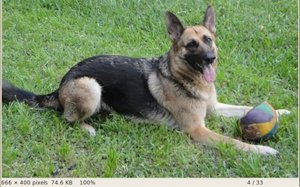
opencv/sources/doc/tutorials/imgproc/imgtrans/remap/images/Remap_Tutorial_Original_Image.jpg
