AndrewDykstra/Face-Tracking-Camera/opencv/sources/doc/tutorials/imgproc/imgtrans/remap/images/Remap_Tutorial_Result_0.jpg

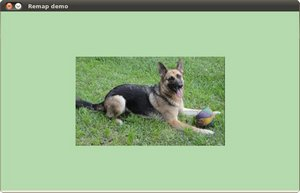
opencv/sources/doc/tutorials/imgproc/imgtrans/remap/images/Remap_Tutorial_Result_0.jpg
