AndrewDykstra/Face-Tracking-Camera/opencv/sources/doc/tutorials/imgproc/imgtrans/remap/images/Remap_Tutorial_Result_1.jpg

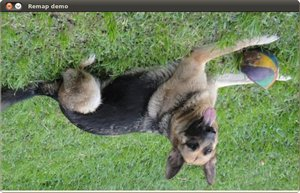
opencv/sources/doc/tutorials/imgproc/imgtrans/remap/images/Remap_Tutorial_Result_1.jpg
