AndrewDykstra/Face-Tracking-Camera/opencv/sources/doc/tutorials/imgproc/imgtrans/sobel_derivatives/images/Sobel_Derivatives_Tutorial_Theory_Intensity_Function.jpg

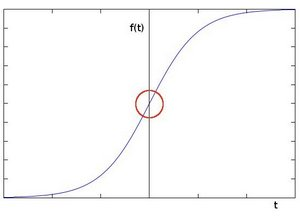
opencv/sources/doc/tutorials/imgproc/imgtrans/sobel_derivatives/images/Sobel_Derivatives_Tutorial_Theory_Intensity_Function.jpg
