AndrewDykstra/Face-Tracking-Camera/opencv/sources/doc/tutorials/imgproc/imgtrans/warp_affine/images/Warp_Affine_Tutorial_Theory_0.jpg

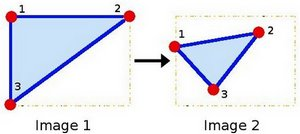
opencv/sources/doc/tutorials/imgproc/imgtrans/warp_affine/images/Warp_Affine_Tutorial_Theory_0.jpg
