AndrewDykstra/Face-Tracking-Camera/opencv/sources/doc/tutorials/imgproc/opening_closing_hats/images/Morphology_2_Tutorial_Theory_TopHat.png

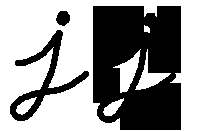
opencv/sources/doc/tutorials/imgproc/opening_closing_hats/images/Morphology_2_Tutorial_Theory_TopHat.png
