AndrewDykstra/Face-Tracking-Camera/opencv/sources/doc/tutorials/imgproc/shapedescriptors/find_contours/images/Find_Contours_Original_Image.jpg

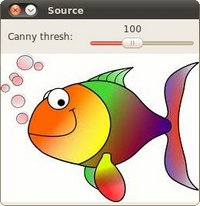
opencv/sources/doc/tutorials/imgproc/shapedescriptors/find_contours/images/Find_Contours_Original_Image.jpg
