AndrewDykstra/Face-Tracking-Camera/opencv/sources/doc/tutorials/imgproc/shapedescriptors/moments/images/Moments_Source_Image.jpg

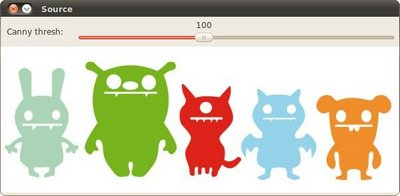
opencv/sources/doc/tutorials/imgproc/shapedescriptors/moments/images/Moments_Source_Image.jpg
