AndrewDykstra/Face-Tracking-Camera/opencv/sources/doc/tutorials/imgproc/threshold/images/Threshold_Tutorial_Cover.jpg

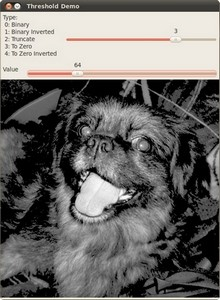
opencv/sources/doc/tutorials/imgproc/threshold/images/Threshold_Tutorial_Cover.jpg
