AndrewDykstra/Face-Tracking-Camera/opencv/sources/doc/tutorials/imgproc/threshold/images/Threshold_Tutorial_Original_Image.jpg

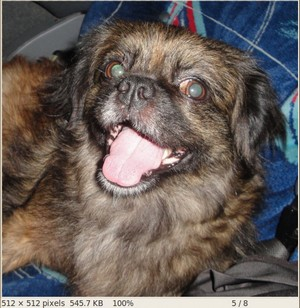
opencv/sources/doc/tutorials/imgproc/threshold/images/Threshold_Tutorial_Original_Image.jpg
