AndrewDykstra/Face-Tracking-Camera/opencv/sources/doc/tutorials/imgproc/threshold/images/Threshold_Tutorial_Result_Zero.jpg

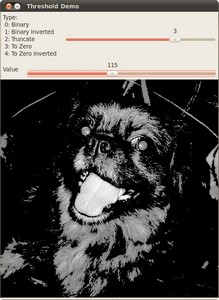
opencv/sources/doc/tutorials/imgproc/threshold/images/Threshold_Tutorial_Result_Zero.jpg
