AndrewDykstra/Face-Tracking-Camera/opencv/sources/doc/tutorials/imgproc/threshold/images/Threshold_Tutorial_Theory_Example.jpg

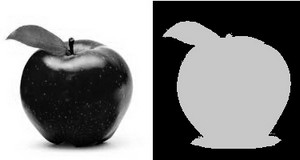
opencv/sources/doc/tutorials/imgproc/threshold/images/Threshold_Tutorial_Theory_Example.jpg
