AndrewDykstra/Face-Tracking-Camera/opencv/sources/doc/tutorials/introduction/android_binary_package/images/android_emulator_opencv_manager_fail.png

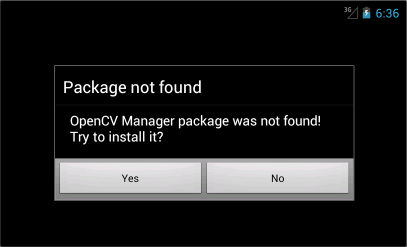
opencv/sources/doc/tutorials/introduction/android_binary_package/images/android_emulator_opencv_manager_fail.png
