AndrewDykstra/Face-Tracking-Camera/opencv/sources/doc/tutorials/introduction/android_binary_package/images/android_package_7zip.png

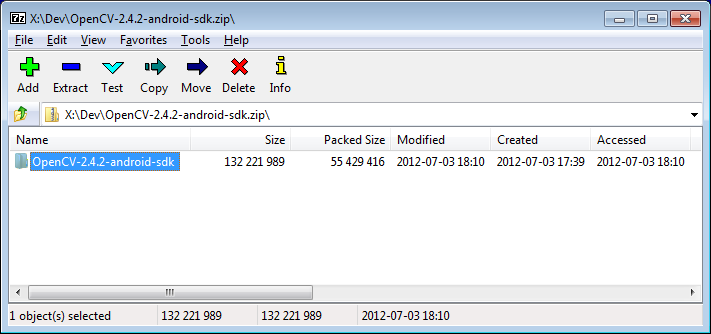
opencv/sources/doc/tutorials/introduction/android_binary_package/images/android_package_7zip.png
