AndrewDykstra/Face-Tracking-Camera/opencv/sources/doc/tutorials/introduction/android_binary_package/images/android_sdk_and_avd_manager.png

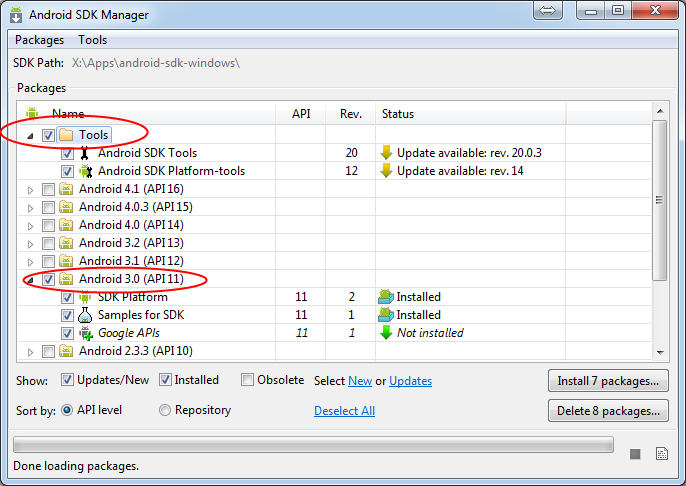
opencv/sources/doc/tutorials/introduction/android_binary_package/images/android_sdk_and_avd_manager.png
