AndrewDykstra/Face-Tracking-Camera/opencv/sources/doc/tutorials/introduction/android_binary_package/images/AVD_create.png

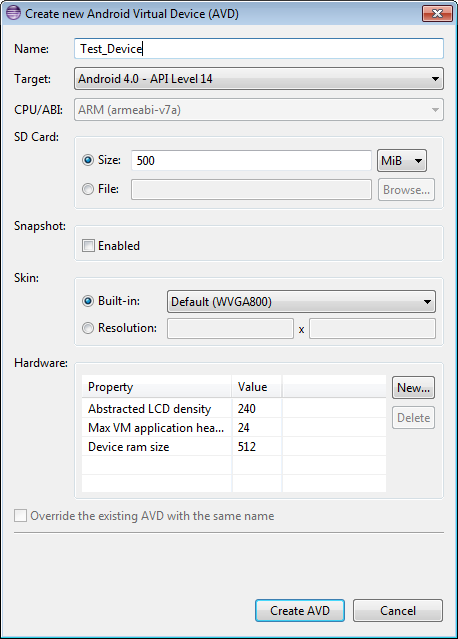
opencv/sources/doc/tutorials/introduction/android_binary_package/images/AVD_create.png
