AndrewDykstra/Face-Tracking-Camera/opencv/sources/doc/tutorials/introduction/android_binary_package/images/AVD_empty.png

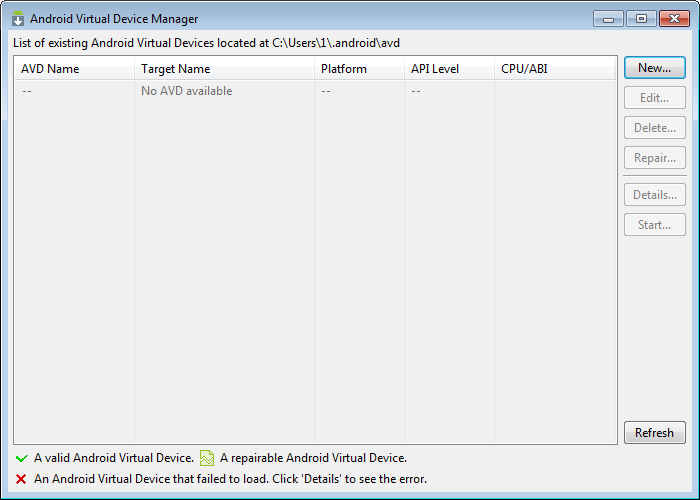
opencv/sources/doc/tutorials/introduction/android_binary_package/images/AVD_empty.png
