AndrewDykstra/Face-Tracking-Camera/opencv/sources/doc/tutorials/introduction/android_binary_package/images/cmd_adb_devices.png

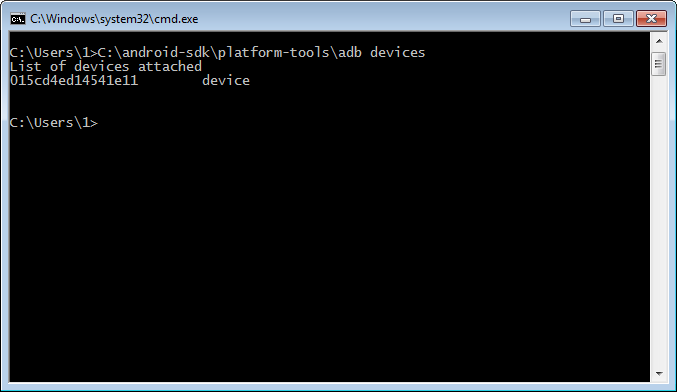
opencv/sources/doc/tutorials/introduction/android_binary_package/images/cmd_adb_devices.png
