AndrewDykstra/Face-Tracking-Camera/opencv/sources/doc/tutorials/introduction/android_binary_package/images/dev_OCV_new_class.png

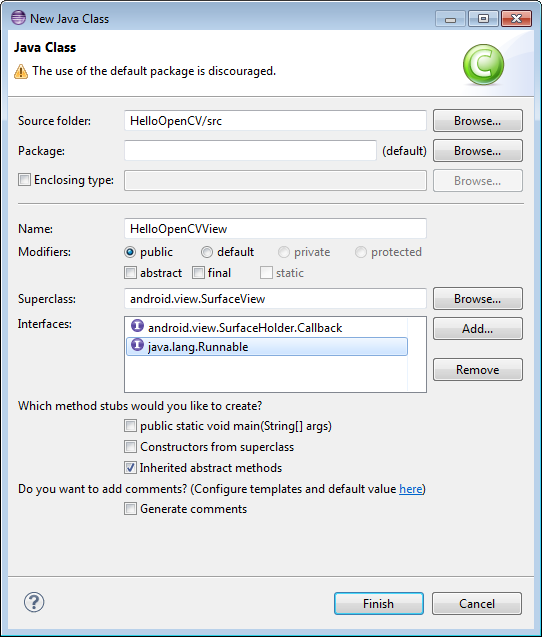
opencv/sources/doc/tutorials/introduction/android_binary_package/images/dev_OCV_new_class.png
