AndrewDykstra/Face-Tracking-Camera/opencv/sources/doc/tutorials/introduction/android_binary_package/images/dev_OCV_reference.png

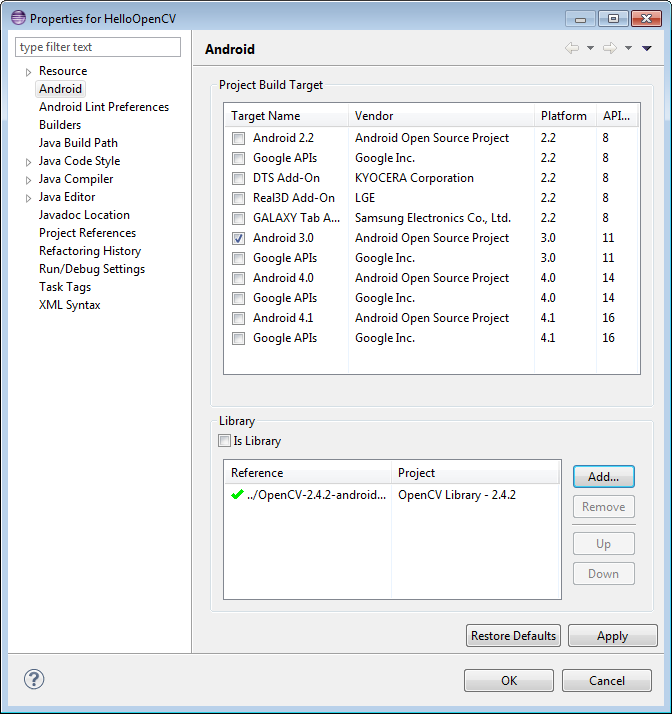
opencv/sources/doc/tutorials/introduction/android_binary_package/images/dev_OCV_reference.png
