AndrewDykstra/Face-Tracking-Camera/opencv/sources/doc/tutorials/introduction/android_binary_package/images/eclipse_1_choose_workspace.png

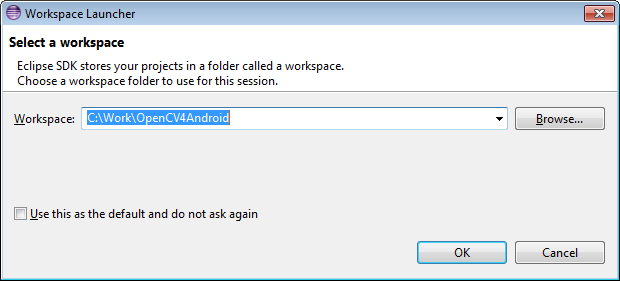
opencv/sources/doc/tutorials/introduction/android_binary_package/images/eclipse_1_choose_workspace.png
