AndrewDykstra/Face-Tracking-Camera/opencv/sources/doc/tutorials/introduction/android_binary_package/images/eclipse_2_window_preferences.png

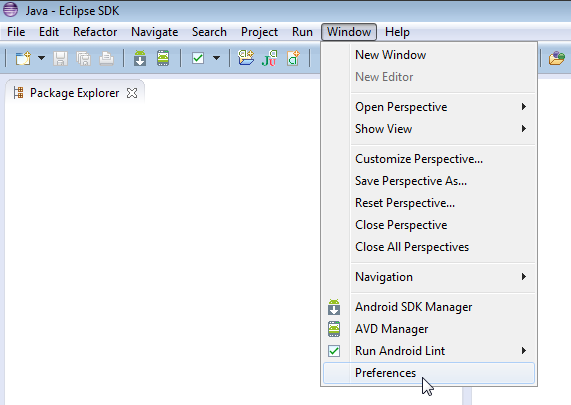
opencv/sources/doc/tutorials/introduction/android_binary_package/images/eclipse_2_window_preferences.png
