AndrewDykstra/Face-Tracking-Camera/opencv/sources/doc/tutorials/introduction/android_binary_package/images/eclipse_6_import_existing_projects.png

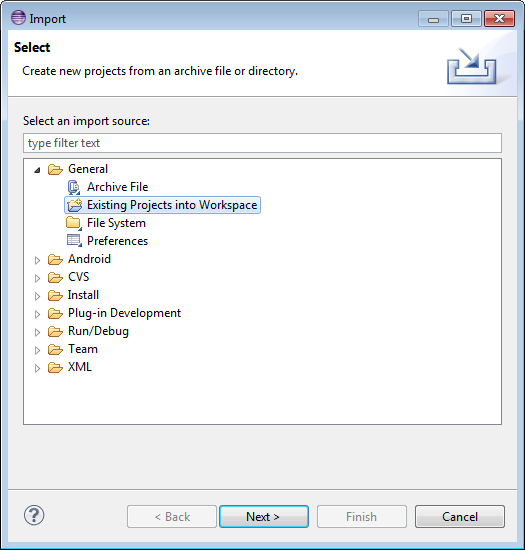
opencv/sources/doc/tutorials/introduction/android_binary_package/images/eclipse_6_import_existing_projects.png
