AndrewDykstra/Face-Tracking-Camera/opencv/sources/doc/tutorials/introduction/android_binary_package/images/eclipse_7_select_projects.png

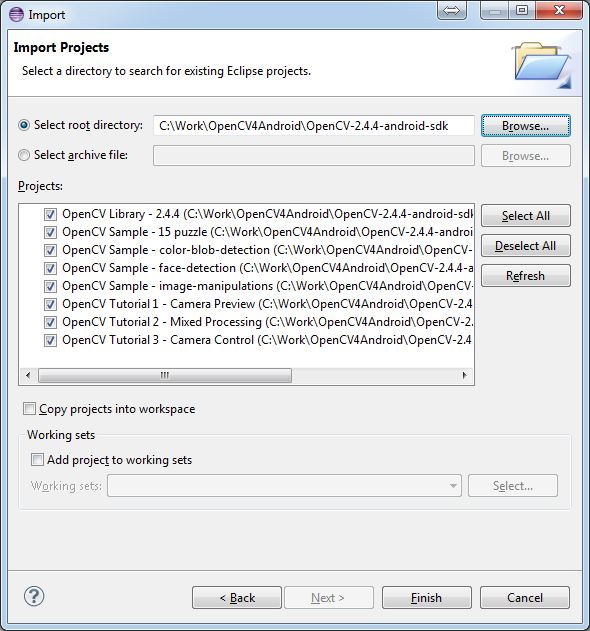
opencv/sources/doc/tutorials/introduction/android_binary_package/images/eclipse_7_select_projects.png
