AndrewDykstra/Face-Tracking-Camera/opencv/sources/doc/tutorials/introduction/android_binary_package/images/eclipse_9_errors_dissapearing.png

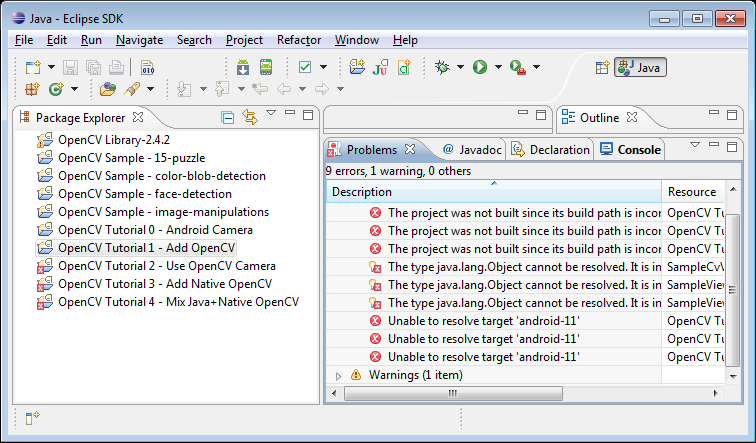
opencv/sources/doc/tutorials/introduction/android_binary_package/images/eclipse_9_errors_dissapearing.png
