AndrewDykstra/Face-Tracking-Camera/opencv/sources/doc/tutorials/introduction/android_binary_package/images/eclipse_11_run_as.png

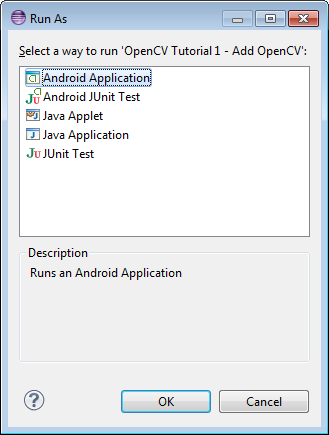
opencv/sources/doc/tutorials/introduction/android_binary_package/images/eclipse_11_run_as.png
