AndrewDykstra/Face-Tracking-Camera/opencv/sources/doc/tutorials/introduction/android_binary_package/images/eclipse_cdt_cfg8.png

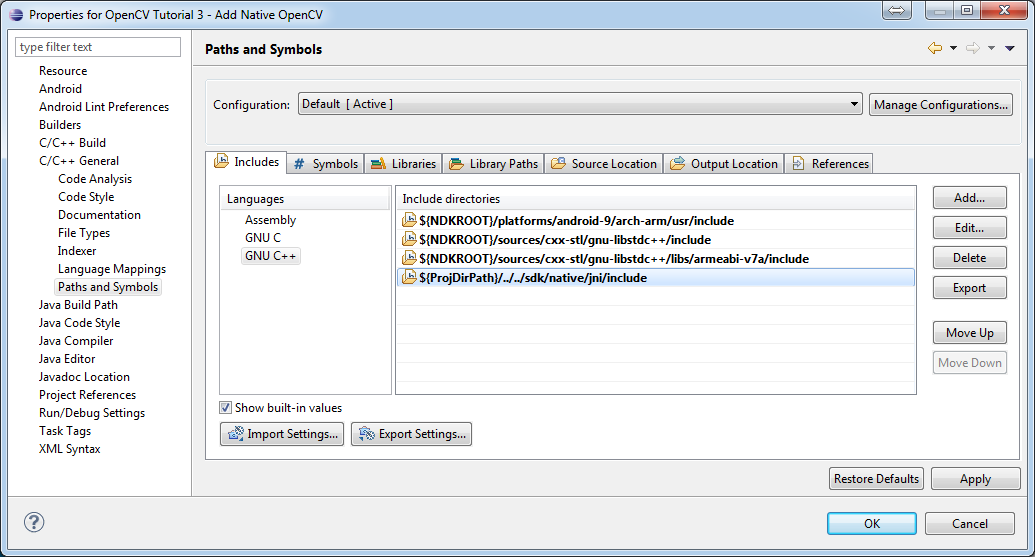
opencv/sources/doc/tutorials/introduction/android_binary_package/images/eclipse_cdt_cfg8.png
