AndrewDykstra/Face-Tracking-Camera/opencv/sources/doc/tutorials/introduction/android_binary_package/images/eclipse_edit_configuration_build_resources.png

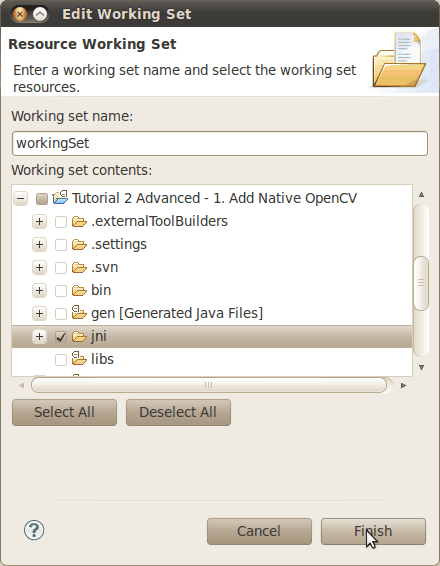
opencv/sources/doc/tutorials/introduction/android_binary_package/images/eclipse_edit_configuration_build_resources.png
