AndrewDykstra/Face-Tracking-Camera/opencv/sources/doc/tutorials/introduction/android_binary_package/images/eclipse_inst_adt.png

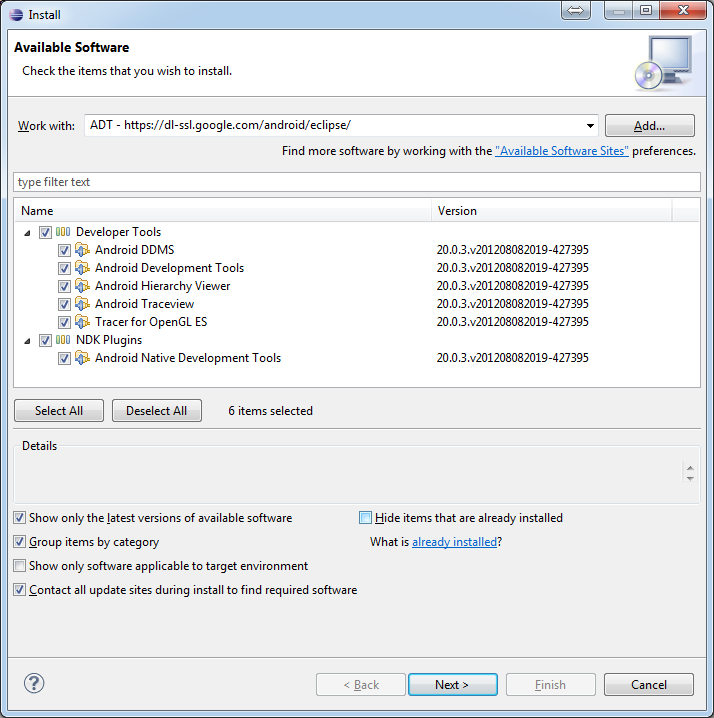
opencv/sources/doc/tutorials/introduction/android_binary_package/images/eclipse_inst_adt.png
