AndrewDykstra/Face-Tracking-Camera/opencv/sources/doc/tutorials/introduction/android_binary_package/images/eclipse_inst_cdt.png

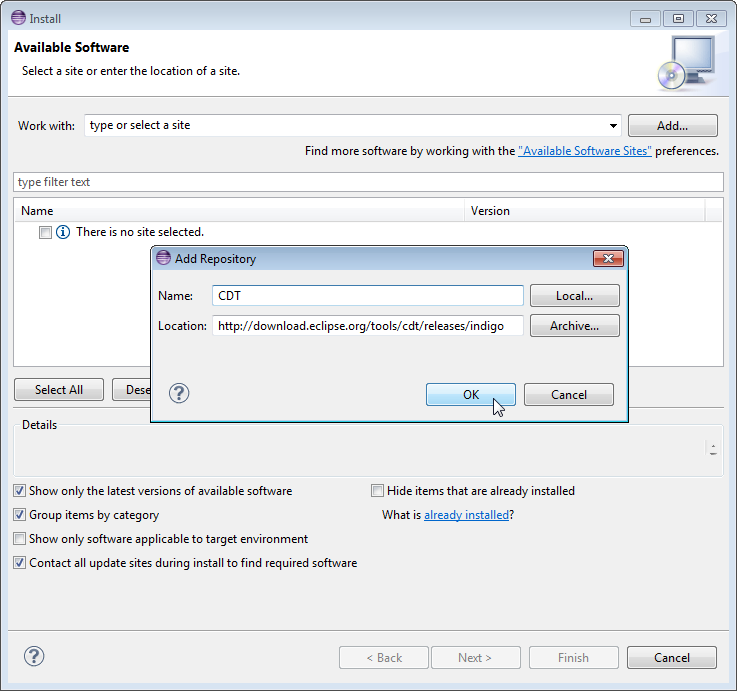
opencv/sources/doc/tutorials/introduction/android_binary_package/images/eclipse_inst_cdt.png
