AndrewDykstra/Face-Tracking-Camera/opencv/sources/doc/tutorials/introduction/android_binary_package/images/eclipse_ndk_build.png

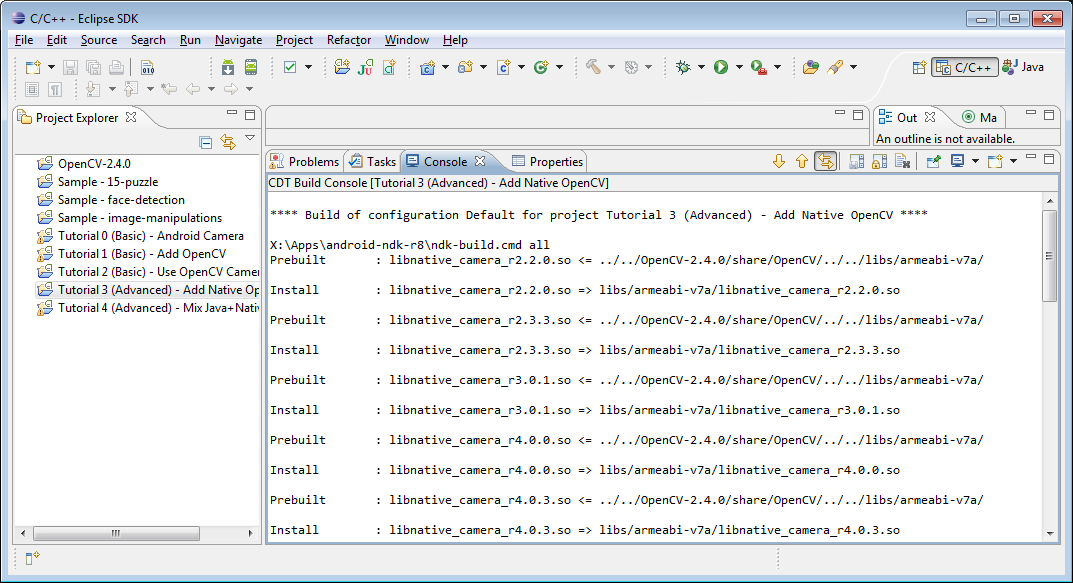
opencv/sources/doc/tutorials/introduction/android_binary_package/images/eclipse_ndk_build.png
