AndrewDykstra/Face-Tracking-Camera/opencv/sources/doc/tutorials/introduction/android_binary_package/images/eclipse_windows_environment.png

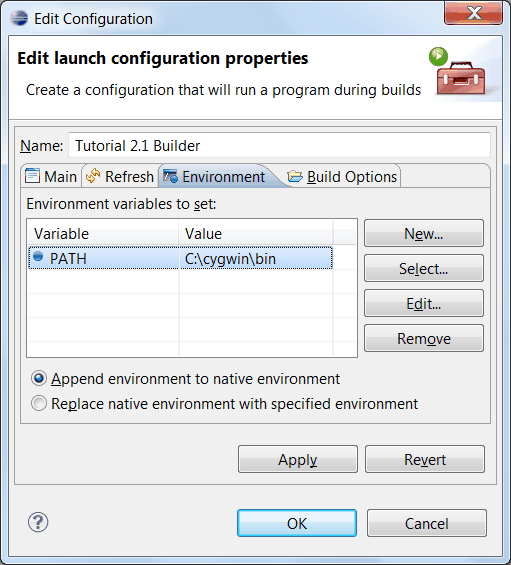
opencv/sources/doc/tutorials/introduction/android_binary_package/images/eclipse_windows_environment.png
