AndrewDykstra/Face-Tracking-Camera/opencv/sources/doc/tutorials/introduction/android_binary_package/images/emulator_canny.png

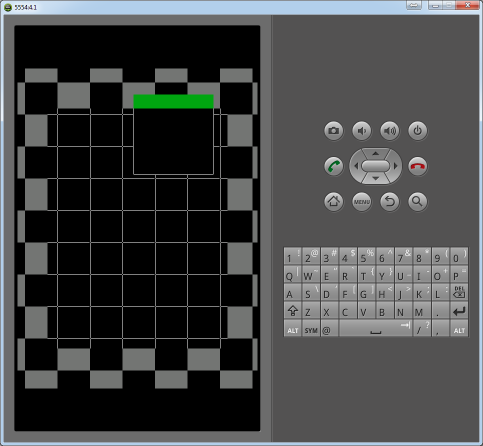
opencv/sources/doc/tutorials/introduction/android_binary_package/images/emulator_canny.png
