AndrewDykstra/Face-Tracking-Camera/opencv/sources/doc/tutorials/introduction/android_binary_package/images/usb_device_connect_08.png

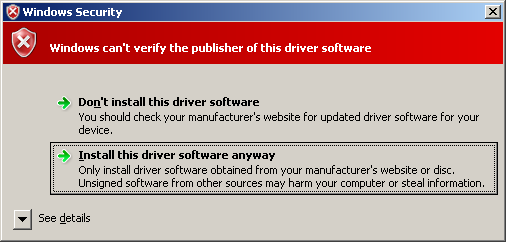
opencv/sources/doc/tutorials/introduction/android_binary_package/images/usb_device_connect_08.png
