AndrewDykstra/Face-Tracking-Camera/opencv/sources/doc/tutorials/introduction/clojure_dev_intro/images/blurred.png

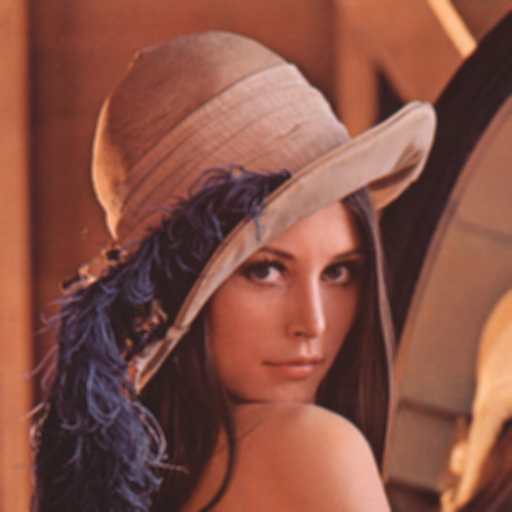
opencv/sources/doc/tutorials/introduction/clojure_dev_intro/images/blurred.png
