AndrewDykstra/Face-Tracking-Camera/opencv/sources/doc/tutorials/introduction/desktop_java/images/ant_output.png

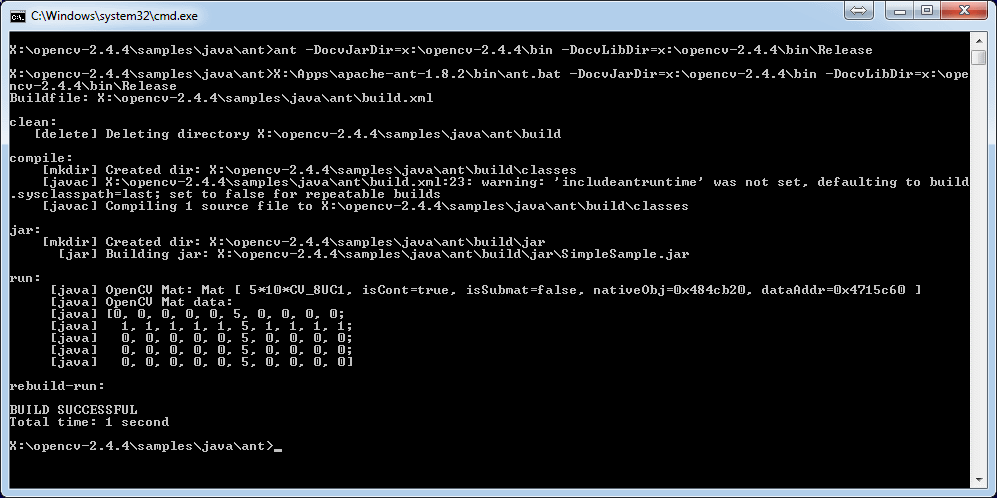
opencv/sources/doc/tutorials/introduction/desktop_java/images/ant_output.png
