AndrewDykstra/Face-Tracking-Camera/opencv/sources/doc/tutorials/introduction/desktop_java/images/sbt_run.png

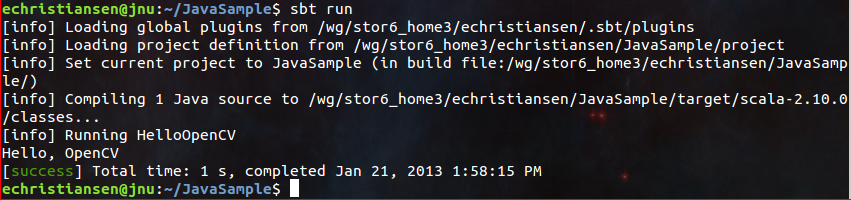
opencv/sources/doc/tutorials/introduction/desktop_java/images/sbt_run.png
