AndrewDykstra/Face-Tracking-Camera/opencv/sources/doc/tutorials/introduction/java_eclipse/images/2-user-library-new.png

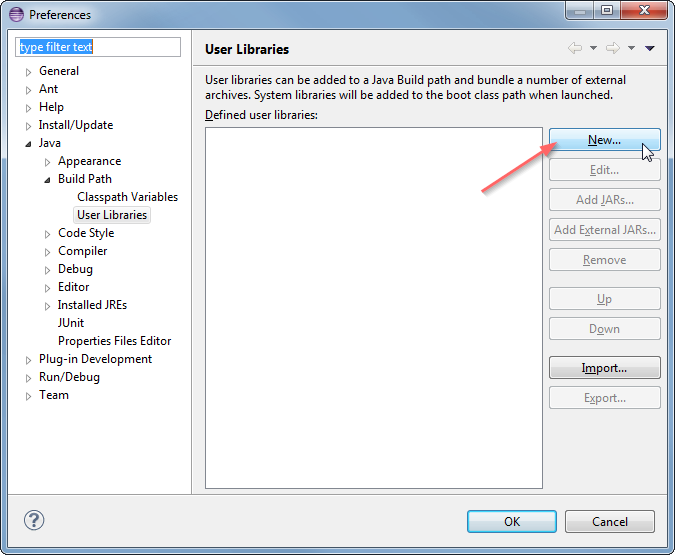
opencv/sources/doc/tutorials/introduction/java_eclipse/images/2-user-library-new.png
