AndrewDykstra/Face-Tracking-Camera/opencv/sources/doc/tutorials/introduction/java_eclipse/images/3-library-name.png

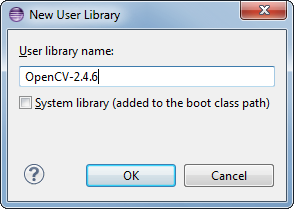
opencv/sources/doc/tutorials/introduction/java_eclipse/images/3-library-name.png
