AndrewDykstra/Face-Tracking-Camera/opencv/sources/doc/tutorials/introduction/java_eclipse/images/4-add-external-jars.png

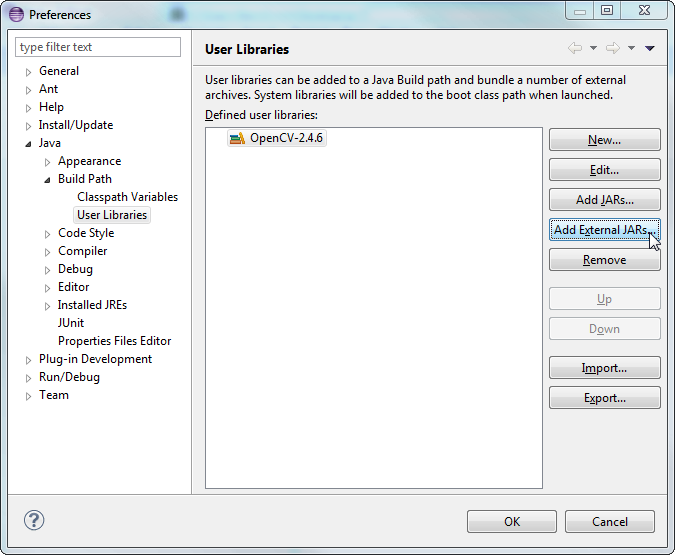
opencv/sources/doc/tutorials/introduction/java_eclipse/images/4-add-external-jars.png
