AndrewDykstra/Face-Tracking-Camera/opencv/sources/doc/tutorials/introduction/java_eclipse/images/6-external-folder.png

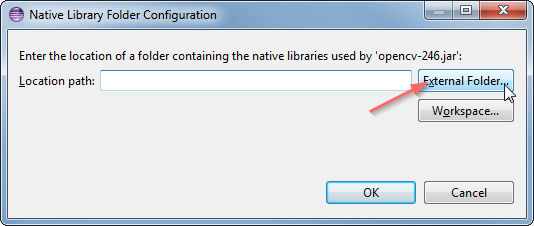
opencv/sources/doc/tutorials/introduction/java_eclipse/images/6-external-folder.png
