AndrewDykstra/Face-Tracking-Camera/opencv/sources/doc/tutorials/introduction/java_eclipse/images/7-user-library-final.png

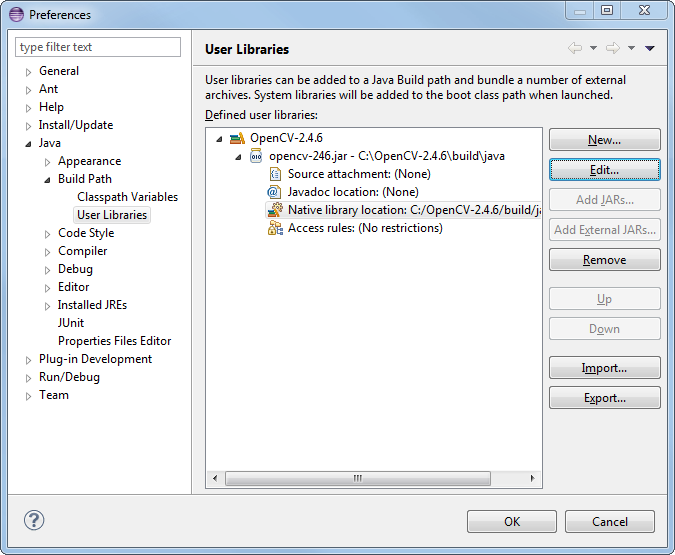
opencv/sources/doc/tutorials/introduction/java_eclipse/images/7-user-library-final.png
