AndrewDykstra/Face-Tracking-Camera/opencv/sources/doc/tutorials/introduction/java_eclipse/images/9-select-user-lib.png

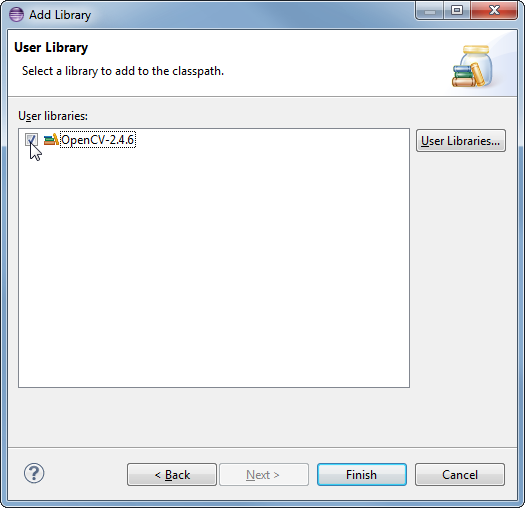
opencv/sources/doc/tutorials/introduction/java_eclipse/images/9-select-user-lib.png
