AndrewDykstra/Face-Tracking-Camera/opencv/sources/doc/tutorials/introduction/java_eclipse/images/10-new-project-created.png

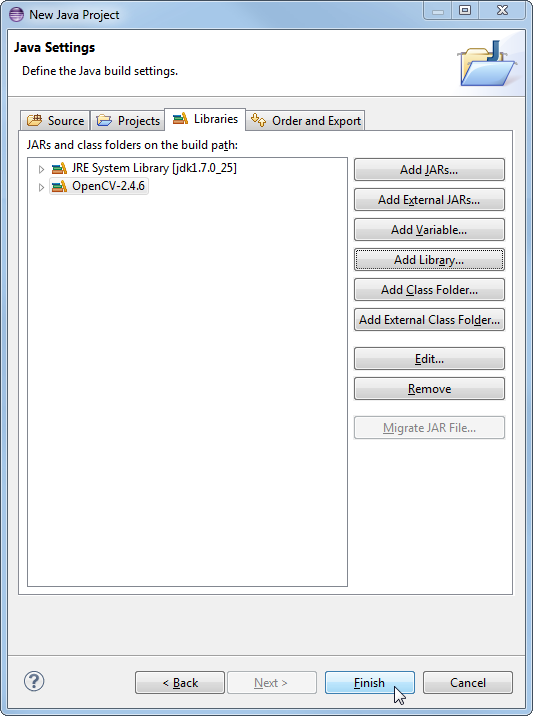
opencv/sources/doc/tutorials/introduction/java_eclipse/images/10-new-project-created.png
