AndrewDykstra/Face-Tracking-Camera/opencv/sources/doc/tutorials/introduction/java_eclipse/images/11-the-code.png

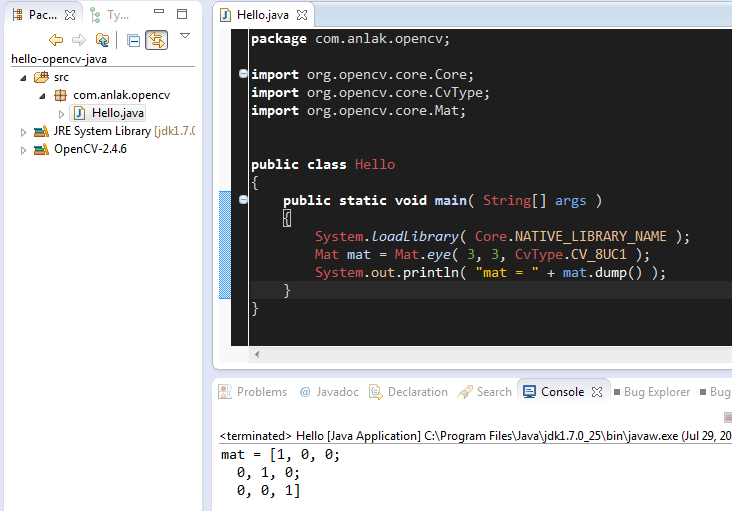
opencv/sources/doc/tutorials/introduction/java_eclipse/images/11-the-code.png
