AndrewDykstra/Face-Tracking-Camera/opencv/sources/doc/tutorials/introduction/linux_eclipse/images/a3.png

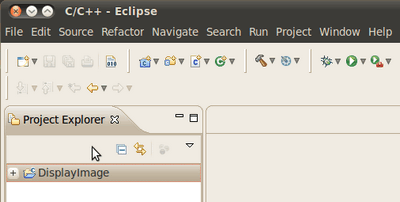
opencv/sources/doc/tutorials/introduction/linux_eclipse/images/a3.png
