AndrewDykstra/Face-Tracking-Camera/opencv/sources/doc/tutorials/introduction/linux_eclipse/images/a9.png

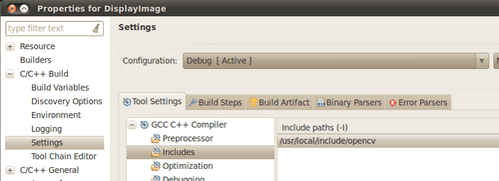
opencv/sources/doc/tutorials/introduction/linux_eclipse/images/a9.png
