AndrewDykstra/Face-Tracking-Camera/opencv/sources/doc/tutorials/introduction/table_of_content_introduction/images/how_to_write_a_tutorial.png

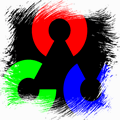
opencv/sources/doc/tutorials/introduction/table_of_content_introduction/images/how_to_write_a_tutorial.png
