AndrewDykstra/Face-Tracking-Camera/opencv/sources/doc/tutorials/introduction/windows_install/images/CMakeBuildOptionsOpenCV.jpg

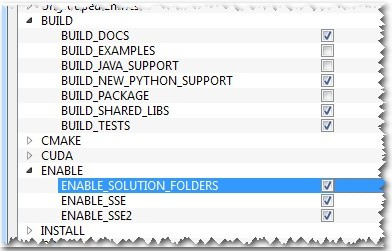
opencv/sources/doc/tutorials/introduction/windows_install/images/CMakeBuildOptionsOpenCV.jpg
