AndrewDykstra/Face-Tracking-Camera/opencv/sources/doc/tutorials/introduction/windows_install/images/CMakeBuildWithWindowsGUI.jpg

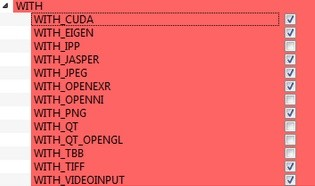
opencv/sources/doc/tutorials/introduction/windows_install/images/CMakeBuildWithWindowsGUI.jpg
