AndrewDykstra/Face-Tracking-Camera/opencv/sources/doc/tutorials/introduction/windows_install/images/IntelTBB.png

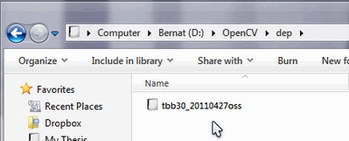
opencv/sources/doc/tutorials/introduction/windows_install/images/IntelTBB.png
