AndrewDykstra/Face-Tracking-Camera/opencv/sources/doc/tutorials/introduction/windows_install/images/MiktexInstall.png

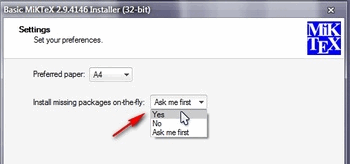
opencv/sources/doc/tutorials/introduction/windows_install/images/MiktexInstall.png
