AndrewDykstra/Face-Tracking-Camera/opencv/sources/doc/tutorials/introduction/windows_install/images/OpenCV_Install_Directory.png

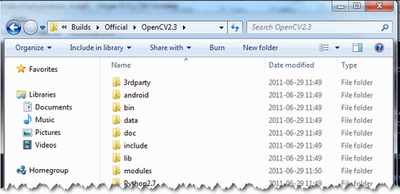
opencv/sources/doc/tutorials/introduction/windows_install/images/OpenCV_Install_Directory.png
