AndrewDykstra/Face-Tracking-Camera/opencv/sources/doc/tutorials/introduction/windows_install/images/OpenCVBuildResultWindows.jpg

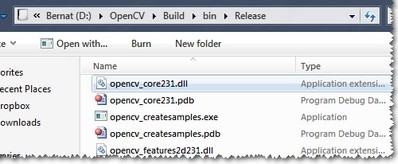
opencv/sources/doc/tutorials/introduction/windows_install/images/OpenCVBuildResultWindows.jpg
