AndrewDykstra/Face-Tracking-Camera/opencv/sources/doc/tutorials/introduction/windows_install/images/qtDownloadThisPackage.png

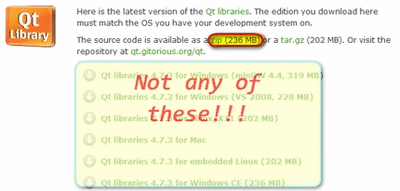
opencv/sources/doc/tutorials/introduction/windows_install/images/qtDownloadThisPackage.png
