AndrewDykstra/Face-Tracking-Camera/opencv/sources/doc/tutorials/introduction/windows_install/images/Sphinx_Install.png

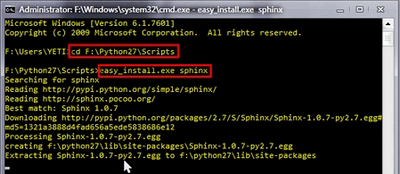
opencv/sources/doc/tutorials/introduction/windows_install/images/Sphinx_Install.png
