AndrewDykstra/Face-Tracking-Camera/opencv/sources/doc/tutorials/introduction/windows_install/images/SVNCheckOutProgress.png

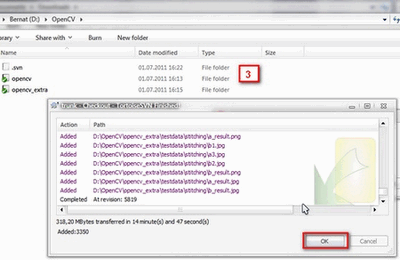
opencv/sources/doc/tutorials/introduction/windows_install/images/SVNCheckOutProgress.png
