AndrewDykstra/Face-Tracking-Camera/opencv/sources/doc/tutorials/introduction/windows_install/images/WindowsQtContoursOutput.png

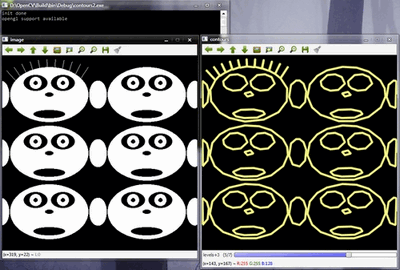
opencv/sources/doc/tutorials/introduction/windows_install/images/WindowsQtContoursOutput.png
