AndrewDykstra/Face-Tracking-Camera/opencv/sources/doc/tutorials/introduction/windows_visual_studio_image_watch/images/breakpoint.png

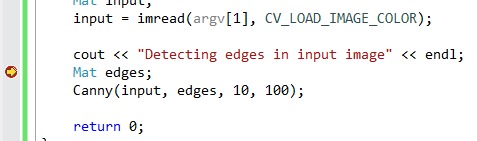
opencv/sources/doc/tutorials/introduction/windows_visual_studio_image_watch/images/breakpoint.png
