AndrewDykstra/Face-Tracking-Camera/opencv/sources/doc/tutorials/introduction/windows_visual_studio_image_watch/images/viewer.jpg

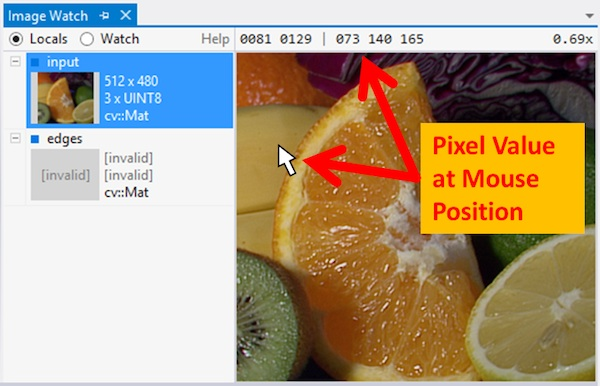
opencv/sources/doc/tutorials/introduction/windows_visual_studio_image_watch/images/viewer.jpg
