AndrewDykstra/Face-Tracking-Camera/opencv/sources/doc/tutorials/introduction/windows_visual_studio_Opencv/images/PropertySheetVS2010.jpg

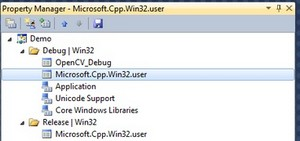
opencv/sources/doc/tutorials/introduction/windows_visual_studio_Opencv/images/PropertySheetVS2010.jpg
