AndrewDykstra/Face-Tracking-Camera/opencv/sources/doc/tutorials/ios/hello/images/header_directive.png

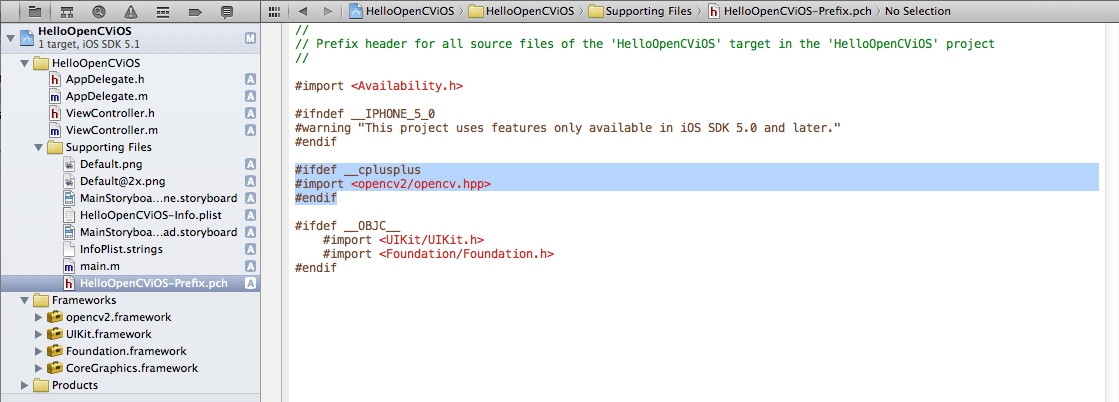
opencv/sources/doc/tutorials/ios/hello/images/header_directive.png
