AndrewDykstra/Face-Tracking-Camera/opencv/sources/doc/tutorials/ios/hello/images/view_did_load.png

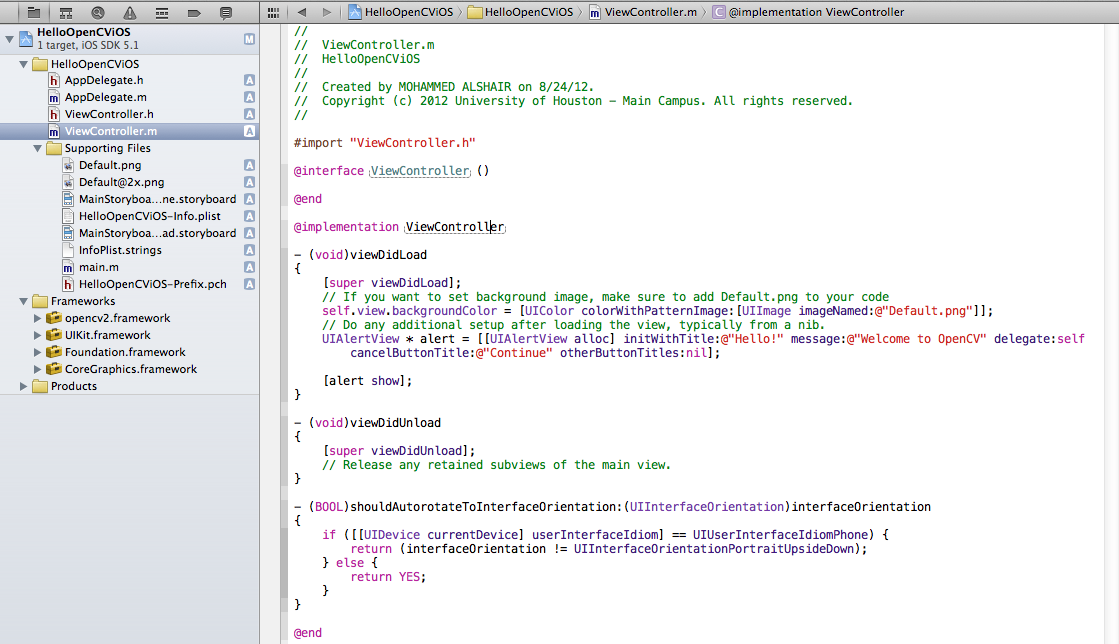
opencv/sources/doc/tutorials/ios/hello/images/view_did_load.png
