AndrewDykstra/Face-Tracking-Camera/opencv/sources/doc/tutorials/ios/image_manipulation/images/output.jpg

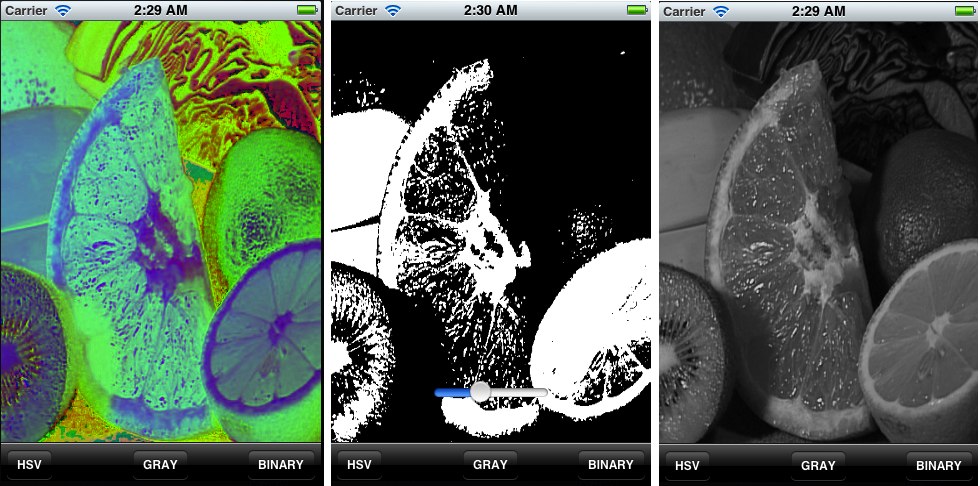
opencv/sources/doc/tutorials/ios/image_manipulation/images/output.jpg
