AndrewDykstra/Face-Tracking-Camera/opencv/sources/doc/tutorials/ios/video_processing/images/xcode_hello_ios_frameworks_add_dependencies.png

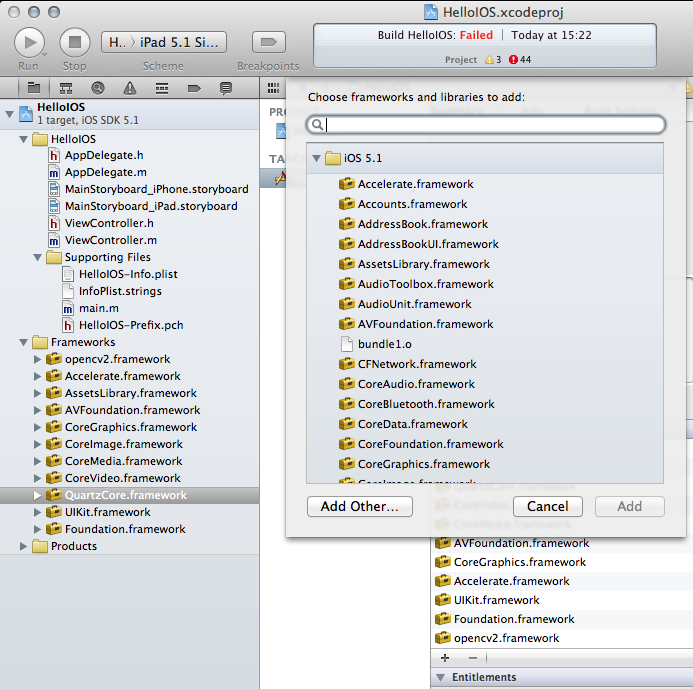
opencv/sources/doc/tutorials/ios/video_processing/images/xcode_hello_ios_frameworks_add_dependencies.png
