AndrewDykstra/Face-Tracking-Camera/opencv/sources/doc/tutorials/ml/non_linear_svms/images/sample-errors-dist.png

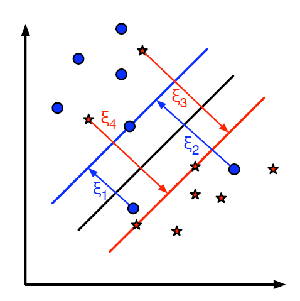
opencv/sources/doc/tutorials/ml/non_linear_svms/images/sample-errors-dist.png
