AndrewDykstra/Face-Tracking-Camera/opencv/sources/doc/tutorials/ml/table_of_content_ml/images/non_linear_svms.png

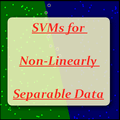
opencv/sources/doc/tutorials/ml/table_of_content_ml/images/non_linear_svms.png
