AndrewDykstra/Face-Tracking-Camera/opencv/sources/doc/tutorials/viz/creating_widgets/images/red_triangle.png

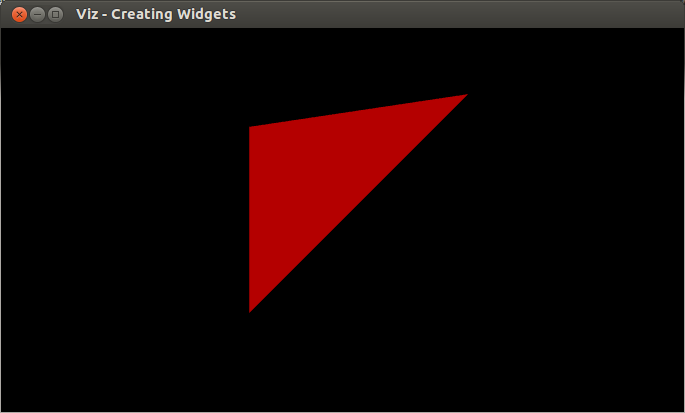
opencv/sources/doc/tutorials/viz/creating_widgets/images/red_triangle.png
