AndrewDykstra/Face-Tracking-Camera/opencv/sources/doc/tutorials/viz/widget_pose/images/widgetpose.png

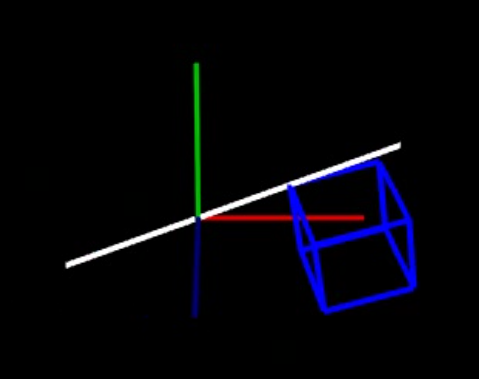
opencv/sources/doc/tutorials/viz/widget_pose/images/widgetpose.png
