AndrewDykstra/Face-Tracking-Camera/opencv/sources/modules/contrib/doc/facerec/img/eigenface_reconstruction_opencv.png

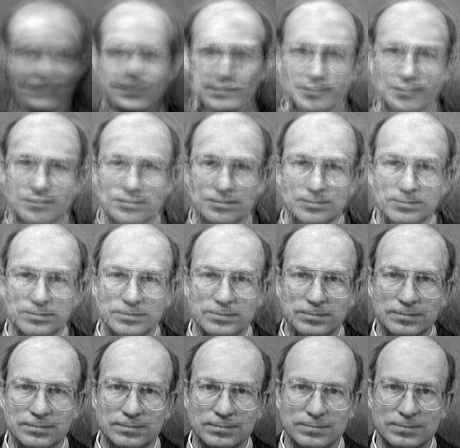
opencv/sources/modules/contrib/doc/facerec/img/eigenface_reconstruction_opencv.png
