AndrewDykstra/Face-Tracking-Camera/opencv/sources/modules/contrib/doc/facerec/img/tutorial/gender_classification/arnie_20_20_200_200.jpg

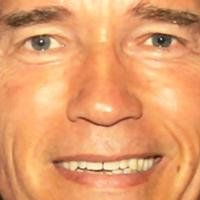
opencv/sources/modules/contrib/doc/facerec/img/tutorial/gender_classification/arnie_20_20_200_200.jpg
