AndrewDykstra/Face-Tracking-Camera/opencv/sources/modules/contrib/doc/facerec/img/tutorial/gender_classification/arnie_30_30_200_200.jpg

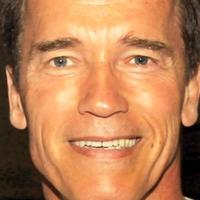
opencv/sources/modules/contrib/doc/facerec/img/tutorial/gender_classification/arnie_30_30_200_200.jpg
