AndrewDykstra/Face-Tracking-Camera/opencv/sources/modules/contrib/doc/facerec/img/tutorial/gender_classification/clooney_set.png

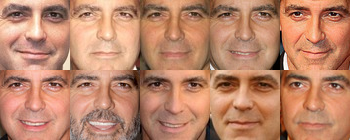
opencv/sources/modules/contrib/doc/facerec/img/tutorial/gender_classification/clooney_set.png
