AndrewDykstra/Face-Tracking-Camera/opencv/sources/modules/contrib/doc/facerec/img/tutorial/gender_classification/fisherface_reconstruction_0.png

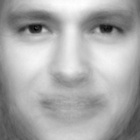
opencv/sources/modules/contrib/doc/facerec/img/tutorial/gender_classification/fisherface_reconstruction_0.png
