AndrewDykstra/Face-Tracking-Camera/opencv/sources/modules/imgproc/doc/pics/building.jpg

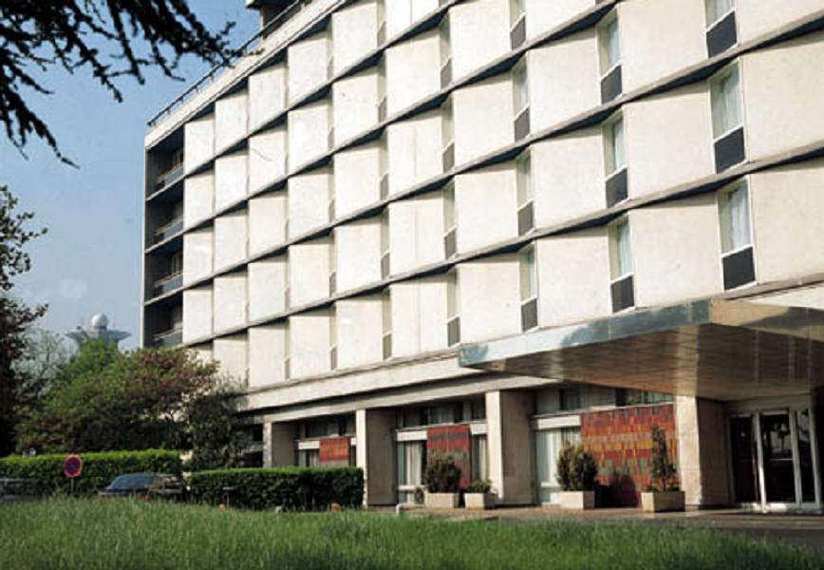
opencv/sources/modules/imgproc/doc/pics/building.jpg
