AndrewDykstra/Face-Tracking-Camera/opencv/sources/platforms/android/service/doc/img/LibInstallAproved.png

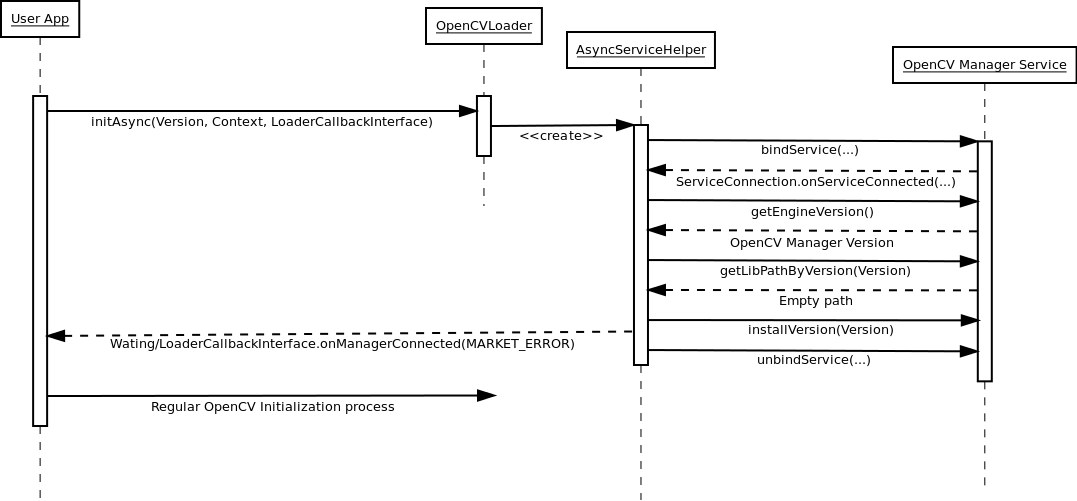
opencv/sources/platforms/android/service/doc/img/LibInstallAproved.png
