AndrewDykstra/Face-Tracking-Camera/opencv/sources/platforms/android/service/doc/img/LibInstallCanceled.png

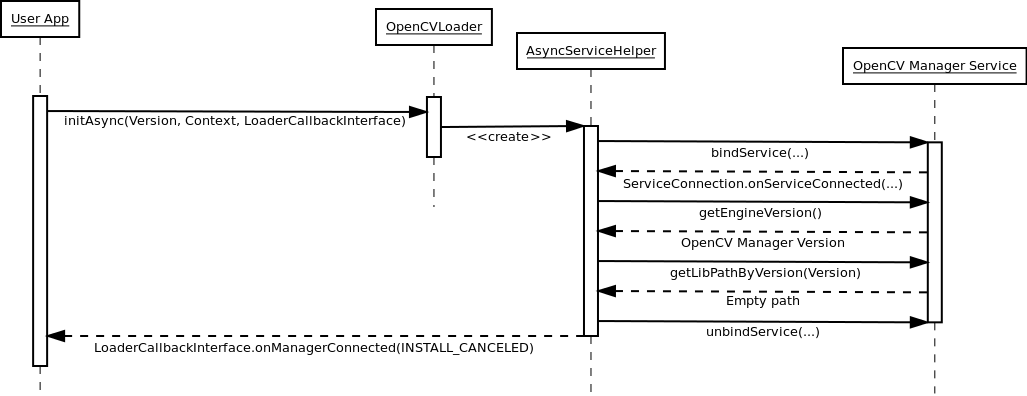
opencv/sources/platforms/android/service/doc/img/LibInstallCanceled.png
