AndrewDykstra/Face-Tracking-Camera/opencv/sources/samples/cpp/tutorial_code/images/baboon.jpg

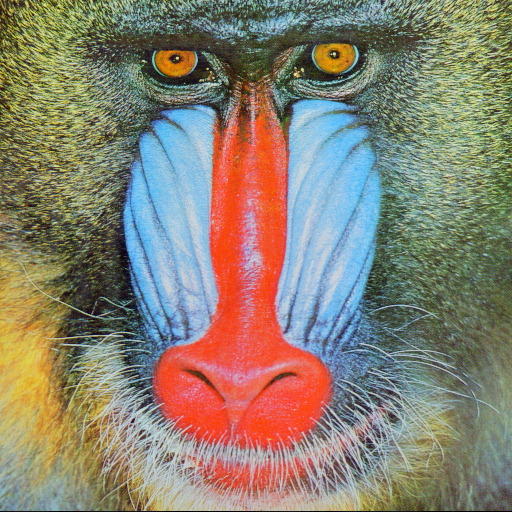
opencv/sources/samples/cpp/tutorial_code/images/baboon.jpg
