AndrewDykstra/Face-Tracking-Camera/opencv/sources/samples/cpp/tutorial_code/images/chicky_512.png

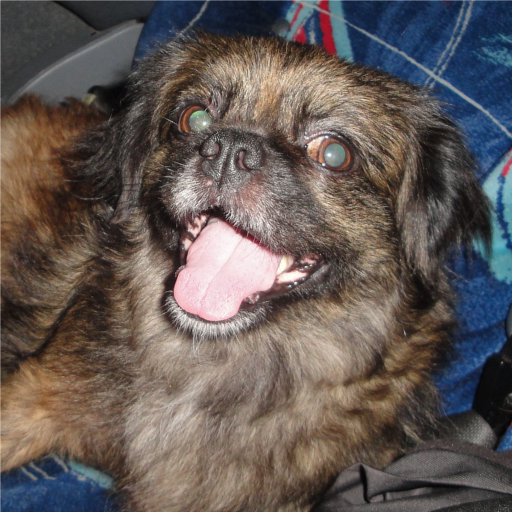
opencv/sources/samples/cpp/tutorial_code/images/chicky_512.png
