AndrewDykstra/Face-Tracking-Camera/opencv/sources/samples/cpp/tutorial_code/images/HappyFish.jpg

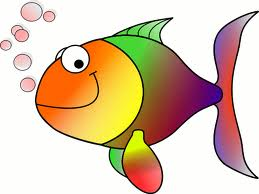
opencv/sources/samples/cpp/tutorial_code/images/HappyFish.jpg
