AndrewDykstra/Face-Tracking-Camera/opencv/sources/samples/cpp/tutorial_code/images/lena.png

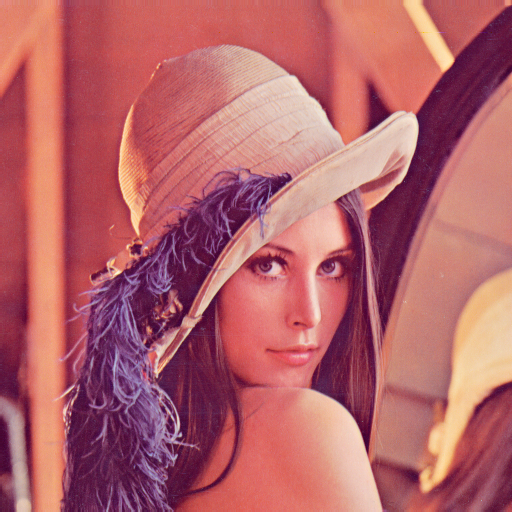
opencv/sources/samples/cpp/tutorial_code/images/lena.png
