AndrewDykstra/Face-Tracking-Camera/opencv/sources/samples/cpp/tutorial_code/images/yellowball.jpg

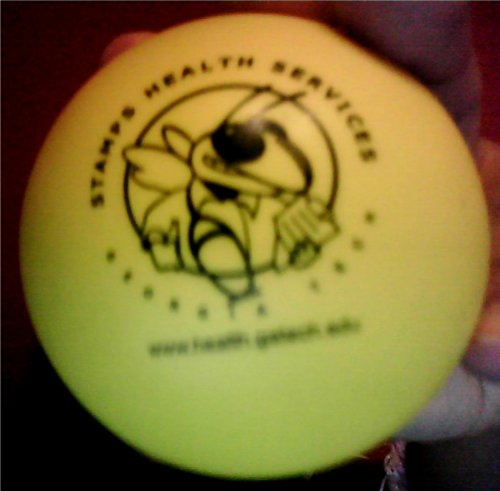
opencv/sources/samples/cpp/tutorial_code/images/yellowball.jpg
