AndrewDykstra/Face-Tracking-Camera/opencv/sources/doc/tutorials/calib3d/camera_calibration/images/fileListImage.jpg

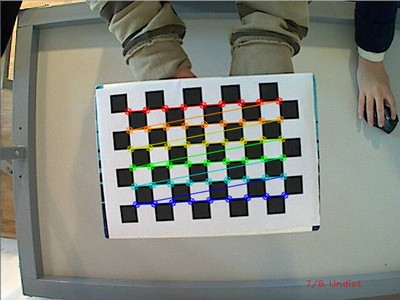
opencv/sources/doc/tutorials/calib3d/camera_calibration/images/fileListImage.jpg
