AndrewDykstra/Face-Tracking-Camera/opencv/sources/doc/tutorials/core/discrete_fourier_transform/images/result_rotated.jpg

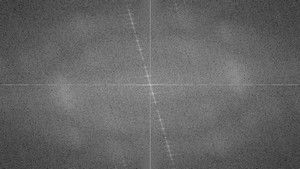
opencv/sources/doc/tutorials/core/discrete_fourier_transform/images/result_rotated.jpg
