AndrewDykstra/Face-Tracking-Camera/opencv/sources/doc/tutorials/features2d/feature_description/images/Feature_Description_BruteForce_Result.jpg

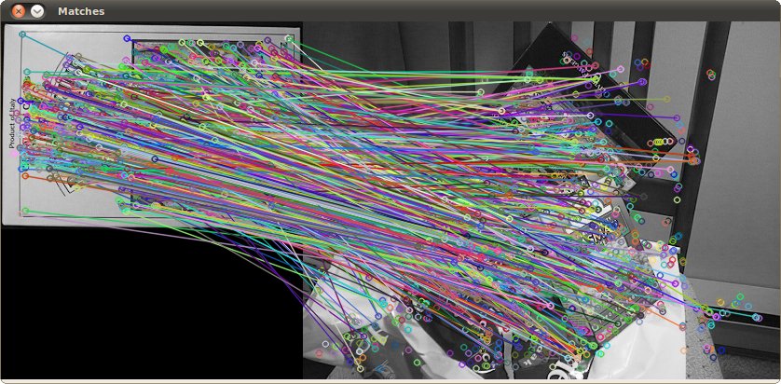
opencv/sources/doc/tutorials/features2d/feature_description/images/Feature_Description_BruteForce_Result.jpg
