AndrewDykstra/Face-Tracking-Camera/opencv/sources/doc/tutorials/features2d/feature_detection/images/Feature_Detection_Result_b.jpg

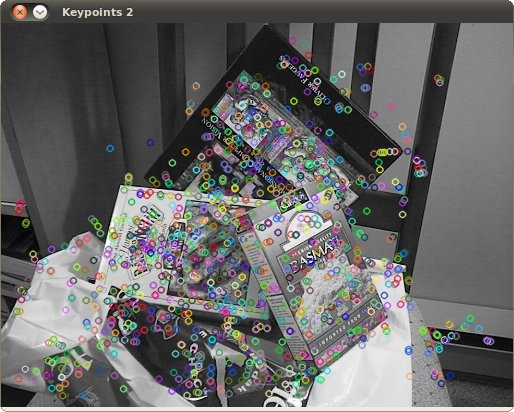
opencv/sources/doc/tutorials/features2d/feature_detection/images/Feature_Detection_Result_b.jpg
