AndrewDykstra/Face-Tracking-Camera/opencv/sources/doc/tutorials/features2d/feature_flann_matcher/images/Feature_FlannMatcher_Keypoints_Result.jpg

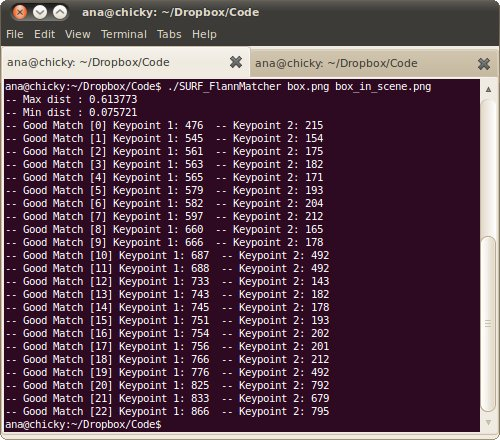
opencv/sources/doc/tutorials/features2d/feature_flann_matcher/images/Feature_FlannMatcher_Keypoints_Result.jpg
