AndrewDykstra/Face-Tracking-Camera/opencv/sources/doc/tutorials/features2d/trackingmotion/generic_corner_detector/images/My_Shi_Tomasi_corner_detector_Result.jpg

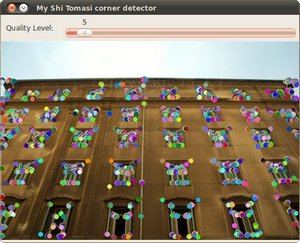
opencv/sources/doc/tutorials/features2d/trackingmotion/generic_corner_detector/images/My_Shi_Tomasi_corner_detector_Result.jpg
