AndrewDykstra/Face-Tracking-Camera/opencv/sources/doc/tutorials/imgproc/histograms/template_matching/images/Template_Matching_Correl_Result_1.jpg

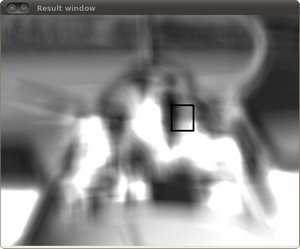
opencv/sources/doc/tutorials/imgproc/histograms/template_matching/images/Template_Matching_Correl_Result_1.jpg
