AndrewDykstra/Face-Tracking-Camera/opencv/sources/doc/tutorials/imgproc/imgtrans/canny_detector/images/Canny_Detector_Tutorial_Result.jpg

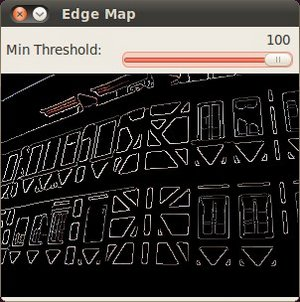
opencv/sources/doc/tutorials/imgproc/imgtrans/canny_detector/images/Canny_Detector_Tutorial_Result.jpg
