AndrewDykstra/Face-Tracking-Camera/opencv/sources/doc/tutorials/imgproc/imgtrans/copyMakeBorder/images/CopyMakeBorder_Tutorial_Results.jpg

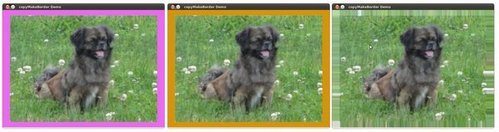
opencv/sources/doc/tutorials/imgproc/imgtrans/copyMakeBorder/images/CopyMakeBorder_Tutorial_Results.jpg
