AndrewDykstra/Face-Tracking-Camera/opencv/sources/doc/tutorials/imgproc/imgtrans/filter_2d/images/filter_2d_tutorial_result.jpg

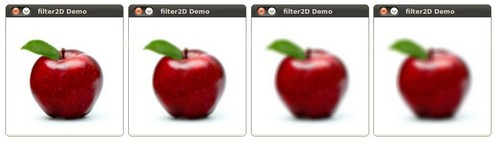
opencv/sources/doc/tutorials/imgproc/imgtrans/filter_2d/images/filter_2d_tutorial_result.jpg
