AndrewDykstra/Face-Tracking-Camera/opencv/sources/doc/tutorials/imgproc/imgtrans/laplace_operator/images/Laplace_Operator_Tutorial_Result.jpg

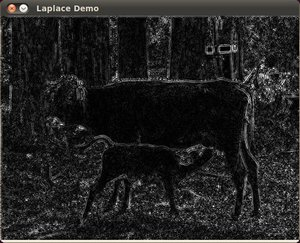
opencv/sources/doc/tutorials/imgproc/imgtrans/laplace_operator/images/Laplace_Operator_Tutorial_Result.jpg
