AndrewDykstra/Face-Tracking-Camera/opencv/sources/doc/tutorials/imgproc/imgtrans/sobel_derivatives/images/Sobel_Derivatives_Tutorial_Result.jpg

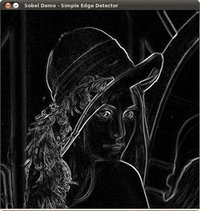
opencv/sources/doc/tutorials/imgproc/imgtrans/sobel_derivatives/images/Sobel_Derivatives_Tutorial_Result.jpg
