AndrewDykstra/Face-Tracking-Camera/opencv/sources/doc/tutorials/imgproc/pyramids/images/Pyramids_Tutorial_PyrUp_Result.jpg

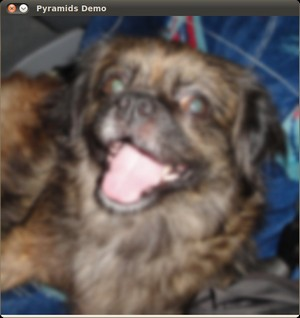
opencv/sources/doc/tutorials/imgproc/pyramids/images/Pyramids_Tutorial_PyrUp_Result.jpg
