AndrewDykstra/Face-Tracking-Camera/opencv/sources/doc/tutorials/imgproc/shapedescriptors/bounding_rects_circles/images/Bounding_Rects_Circles_Result.jpg

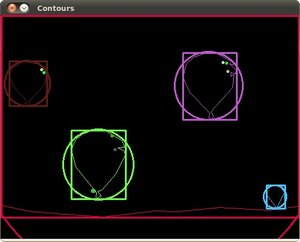
opencv/sources/doc/tutorials/imgproc/shapedescriptors/bounding_rects_circles/images/Bounding_Rects_Circles_Result.jpg
