AndrewDykstra/Face-Tracking-Camera/opencv/sources/doc/tutorials/imgproc/shapedescriptors/bounding_rotated_ellipses/images/Bounding_Rotated_Ellipses_Result.jpg

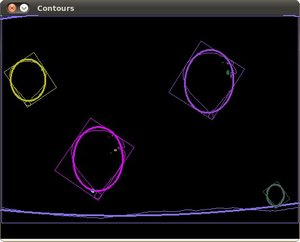
opencv/sources/doc/tutorials/imgproc/shapedescriptors/bounding_rotated_ellipses/images/Bounding_Rotated_Ellipses_Result.jpg
