AndrewDykstra/Face-Tracking-Camera/opencv/sources/doc/tutorials/imgproc/shapedescriptors/hull/images/Hull_Result.jpg

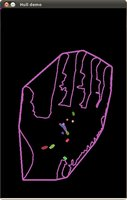
opencv/sources/doc/tutorials/imgproc/shapedescriptors/hull/images/Hull_Result.jpg
