AndrewDykstra/Face-Tracking-Camera/opencv/sources/doc/tutorials/imgproc/shapedescriptors/moments/images/Moments_Result2.jpg

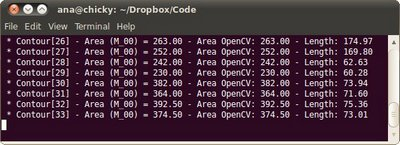
opencv/sources/doc/tutorials/imgproc/shapedescriptors/moments/images/Moments_Result2.jpg
