AndrewDykstra/Face-Tracking-Camera/opencv/sources/doc/tutorials/imgproc/shapedescriptors/point_polygon_test/images/Point_Polygon_Test_Result.jpg

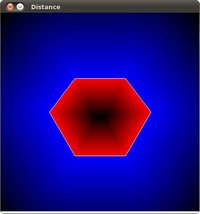
opencv/sources/doc/tutorials/imgproc/shapedescriptors/point_polygon_test/images/Point_Polygon_Test_Result.jpg
