AndrewDykstra/Face-Tracking-Camera/opencv/sources/doc/tutorials/introduction/display_image/images/Display_Image_Tutorial_Result.jpg

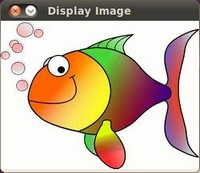
opencv/sources/doc/tutorials/introduction/display_image/images/Display_Image_Tutorial_Result.jpg
