AndrewDykstra/Face-Tracking-Camera/opencv/sources/doc/tutorials/introduction/load_save_image/images/Load_Save_Image_Result_1.jpg

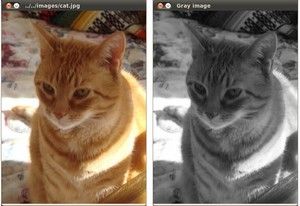
opencv/sources/doc/tutorials/introduction/load_save_image/images/Load_Save_Image_Result_1.jpg
