AndrewDykstra/Face-Tracking-Camera/opencv/sources/doc/tutorials/ml/introduction_to_svm/images/result.png

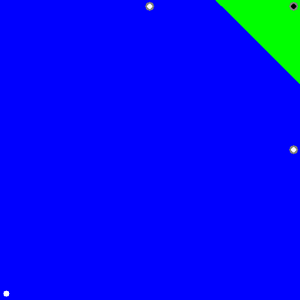
opencv/sources/doc/tutorials/ml/introduction_to_svm/images/result.png
