AndrewDykstra/Face-Tracking-Camera/opencv/sources/doc/tutorials/ml/non_linear_svms/images/result.png

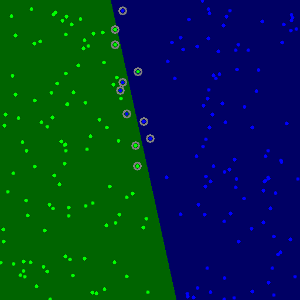
opencv/sources/doc/tutorials/ml/non_linear_svms/images/result.png
