AndrewDykstra/Face-Tracking-Camera/opencv/sources/doc/tutorials/introduction/android_binary_package/images/eclipse_8b_fix_props.png

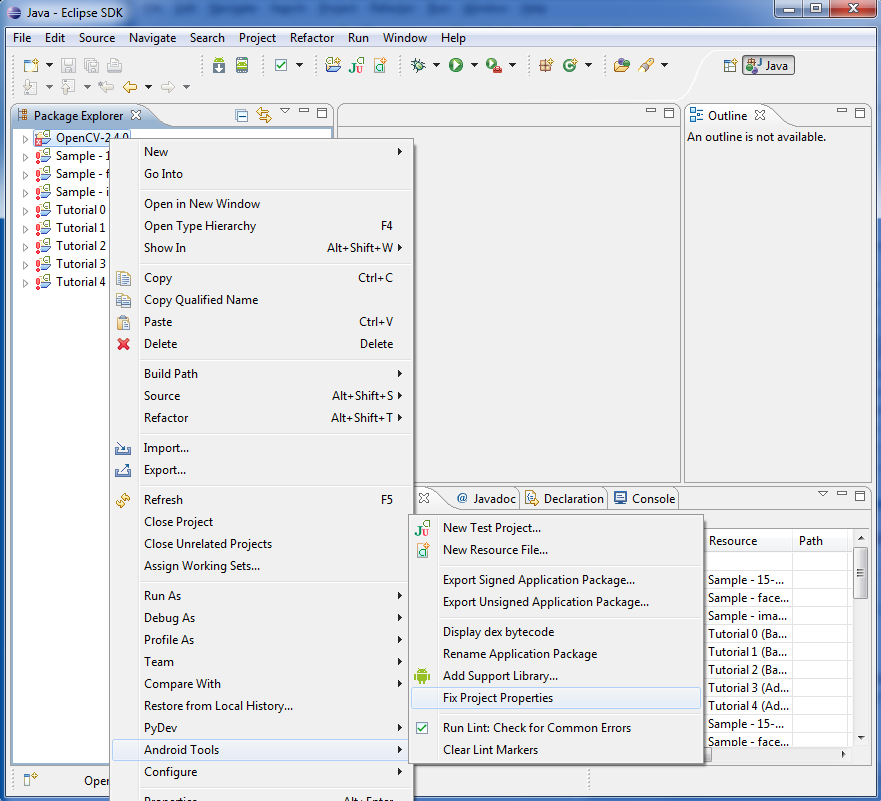
opencv/sources/doc/tutorials/introduction/android_binary_package/images/eclipse_8b_fix_props.png
